pihrt-com/playoff/Playoff app/playoff.py

#!/usr/bin/env python
# playoff.py
# -*- coding: utf-8 -*-
__author__ = 'Martin Pihrt'

APP_current       = "1.0.11"                                         # current version of the application
APP_date          = "23.06.2026-08:15"                               # current version date  
update_check_link = "https://raw.githubusercontent.com/pihrt-com/playoff/refs/heads/main/Playoff%20app/version.json"    # path to JSON with APP version

import tkinter as tk
from tkinter import ttk, simpledialog, messagebox, filedialog, colorchooser
from tkinter import font as tkfont

import math, json, os, sys
import urllib.request
import time

try:
    from reportlab.pdfgen import canvas as rl_canvas
    from reportlab.lib.pagesizes import A4, landscape
    from reportlab.lib.colors import HexColor, black
    from reportlab.pdfbase import pdfmetrics
    from reportlab.pdfbase.ttfonts import TTFont
except ImportError:
    messagebox.showerror(
        "Chyba",
        "Pro vektorový PDF export je potřeba knihovna reportlab:\n\npip install reportlab"
    )

try:
    from openpyxl import Workbook, load_workbook
except ImportError:
    messagebox.showerror(
        "Chyba",
        "Pro import/export excell je potřeba knihovna openpyxl:\n\npip install openpyxl"
    )    

# universal path to resources (works in Python and PyInstaller EXE)
if getattr(sys, 'frozen', False):
    BASE_PATH = sys._MEIPASS
else:
    BASE_PATH = os.path.abspath(os.path.dirname(__file__))

# Pillow optional
try:
    from PIL import Image, ImageDraw, ImageFont, ImageTk
    PIL_AVAILABLE = True
except Exception:
    PIL_AVAILABLE = False

# try import usb_module (the new module we added). If missing, we provide a stub.
# Always add the current folder to sys.path so that the local usb_module.py is loaded.
sys.path.insert(0, os.path.dirname(os.path.abspath(__file__)))

try:
    import usb_module   # C:\Playoff\usb_module.py
    USB_AVAILABLE = True
except Exception as e:
    self._log("USB module error:", e)
    usb_module = None
    USB_AVAILABLE = False

# default settings
DEFAULT_BOX_W = 180
DEFAULT_BOX_H = 30
DEFAULT_H_GAP = 200
DEFAULT_V_GAP = 10
LINE_COLOR = "#0b6bd6"              # blue color
THIRD_PLACE_LINE_COLOR = "#d62828"  # red color
BOX_FILL = "#ffffff"
BOX_OUTLINE = "#000000"
TITLE_COLOR = "#000000"
CANVAS_BG_DEFAULT = "#ffffff"
# vítěz
WINNER_FILL = "#ffe06a"
WINNER_OUTLINE = "#cc9a00"
WINNER_TEXT_COLOR = "#000000"

# Default USB settings defaults (kept in setup file)
DEFAULT_USB_PORT           = ""
DEFAULT_USB_BAUD           = 115200
DEFAULT_USB_TIMEOUT        = 10.0

DEFAULT_USB_DISPLAY_A_BAUD = 115200
DEFAULT_USB_DISPLAY_B_BAUD = 115200

# --- Data classes ---
class Slot:
    def __init__(self, text=""):
        self.text = text

class Match:
    def __init__(self, a=None, b=None):
        self.a = a if a else Slot()
        self.b = b if b else Slot()

class Bracket:
    def __init__(self, team_list, pre_round_list, use_pre_round=False):
        """team_list: list of initial team names (may be empty strings)"""
        self.use_pre_round = use_pre_round
        self.team_count = max(0, int(len(team_list)))
        self.pre_count = max(0, int(len(pre_round_list)))
        self.rounds = []  # list of lists of Match
        self.titles = []
        self.pre_rounds = []
        self.pre_titles = []
        if use_pre_round:
            self._build_pre(pre_round_list)
        self._build(team_list)

    def _build_pre(self, pre_round_list):
        self.pre_rounds = []
        self.pre_titles = ["Předkolo"]
        first_round_match_count = math.ceil(len(pre_round_list) / 2)
        matches = []
        for i in range(first_round_match_count):
            matches.append(Match(Slot(""), Slot("")))
        self.pre_rounds.append(matches)

    def _build(self, team_list):
        self.rounds = []
        self.titles = []
        # initial round: pair teams sequentially, allowing last single
        teams = list(team_list)
        teams = [str(t) if t is not None else "" for t in teams]

        # first round matches: ceil(n/2)
        first_matches = math.ceil(len(teams) / 2) if len(teams) > 0 else 1
        matches0 = []
        for i in range(first_matches):
            a_idx = 2 * i
            b_idx = 2 * i + 1
            a = Slot(teams[a_idx]) if a_idx < len(teams) else Slot("")
            b = Slot(teams[b_idx]) if b_idx < len(teams) else Slot("")
            matches0.append(Match(a, b))
        self.rounds.append(matches0)
        self.titles.append("Kolo 1")

        # build subsequent rounds until 1 match
        prev_matches = matches0
        r = 1
        while len(prev_matches) > 1:
            next_count = math.ceil(len(prev_matches) / 2)
            next_matches = [Match() for _ in range(next_count)]
            self.rounds.append(next_matches)
            # default title
            if next_count == 1:
                self.titles.append("Finále")
            else:
                self.titles.append(f"Kolo {r+1}")
            prev_matches = next_matches
            r += 1
        # --- Winner ---
        # last real round = final → add a round with one slot
        winner_match = Match(Slot(""), Slot(""))
        self.rounds.append([winner_match])
        self.titles.append("Vítěz")            

    def rounds_count(self):
        return len(self.rounds)

# --- App ---
class PlayoffApp:
    def __init__(self, root):
        self.root = root
        root.title("Playoff generátor by Martin Pihrt © www.pihrt.com")

        # state
        self.bracket = None
        self.current_winner = ""
        self.bg_path = None
        self.bg_image = None
        self.bg_tk = None
        self.canvas_bg = CANVAS_BG_DEFAULT
        self.line_width = 2           # normal/thick
        self.font_scale = "large"     # small/medium/large
        self.odd_behavior = "manual"  # auto/manual/waiting
        self.lock_edit = False
        self.projector_mode = False
        self.enable_timer = True
        self.timer_value = '05:00'
        self.timer_running = False
        self.timer_blink = False
        self.current_seconds = 0
        self.timer_start_mode = "ok"  # "start" | "ok"  
        self.team_names = []          # Team naming database
        self.pre_round_enabled = True
        self.third_place_enabled = True
        self.third_place_title = "3. místo"
        self.lap_timer_enabled = True
        self.lap_timer_var = tk.BooleanVar(value=self.lap_timer_enabled)
        self.lap_time_a = 0   # ms
        self.lap_time_b = 0   # ms
        self.lap_time_a_var = tk.StringVar(value="A 00:00:000")
        self.lap_time_b_var = tk.StringVar(value="B 00:00:000")
        self.lap_running_a = False
        self.lap_running_b = False
        self.lap_after_id = None        
        self.font_scale_var = tk.StringVar(value=self.font_scale)
        self.odd_behavior_var = tk.StringVar(value=self.odd_behavior)
        self.line_width_var = tk.IntVar(value=self.line_width)
        self.timer_menu_var = tk.BooleanVar(value=self.enable_timer)
        self.timer_start_mode_var = tk.StringVar(value=self.timer_start_mode)
        self.pre_round_var = tk.BooleanVar(value=self.pre_round_enabled)
        self.third_place_var = tk.BooleanVar(value=self.third_place_enabled)

        self.third_place = {"a": "", "b": "", "winner": ""}        

        # USB manager (from usb_module)
        if USB_AVAILABLE:
            try:
                self.usb = usb_module.USBManager(self)
            except Exception:
                self.usb = None
        else:
            self.usb = None
        # store usb settings for saving into setup file
        self.usb_port = DEFAULT_USB_PORT
        self.usb_baud = DEFAULT_USB_BAUD
        self.usb_timeout = DEFAULT_USB_TIMEOUT

        # 7 seg LED display
        self.display_port_a = ""
        self.display_port_b = ""
        self.display_baud_a = DEFAULT_USB_DISPLAY_A_BAUD
        self.display_baud_b = DEFAULT_USB_DISPLAY_B_BAUD

        # view mode
        self.view_mode = "playoff"
        self.view_mode_var = tk.StringVar(value=self.view_mode)
        
        # laps mode data
        self.laps_a = []
        self.laps_b = []
        self.lap_id_a = 1
        self.lap_id_b = 1

        # Top toolbar: left settings (calls existing menu), right Start button and status label
        toolbar = tk.Frame(root)
        toolbar.pack(side='top', fill='x', padx=4, pady=4)

        # --- Settings icon (gear wheel) ---
        try:
            settings_img_path = os.path.join(BASE_PATH, "settings.ico")

            if PIL_AVAILABLE:
                img = Image.open(settings_img_path)

                if hasattr(img, "n_frames"):
                    best_pixels = 0
                    best_frame = 0
                    for i in range(img.n_frames):
                        img.seek(i)
                        w, h = img.size
                        if w * h > best_pixels:
                            best_pixels = w * h
                            best_frame = i
                    img.seek(best_frame)

                TARGET_H = 44

                w, h = img.size
                scale = TARGET_H / h
                new_w = int(w * scale)
                new_h = int(h * scale)

                img = img.resize((new_w, new_h), Image.LANCZOS)
                settings_raw = ImageTk.PhotoImage(img)

            else:
                # fallback bez Pillow
                settings_raw = tk.PhotoImage(file=settings_img_path)

            self.settings_btn = tk.Menubutton(toolbar, image=settings_raw, relief=tk.FLAT)
            self.settings_btn.image = settings_raw  # nutné pro garbage-collector

            self.settings_menu = tk.Menu(self.settings_btn, tearoff=0)
            self.settings_btn.config(menu=self.settings_menu)
            self.settings_btn.pack(side='left', padx=4)

            ver_txt = f"app verze: {APP_current} ({APP_date})"
            self.ver_label = tk.Label(toolbar, text=ver_txt, fg="#666666", font=("Arial", 7))
            self.ver_label.pack(side='left', padx=(10,0))

            # --- USB STATUS INDICATOR ---
            self.usb_status_canvas = tk.Canvas(toolbar, width=12, height=12, highlightthickness=0, bd=0, bg=toolbar.cget("bg"))
            self.usb_status_id = self.usb_status_canvas.create_oval(2, 2, 10, 10, fill="red", outline="red")
            self.usb_status_canvas.pack(side="left", padx=(10, 2))

            self.usb_status_label = tk.Label(toolbar, text="USB", fg="#333333", font=("Arial", 8, "bold"))
            self.usb_status_label.pack(side="left", padx=(0, 10))

            # --- DISPLAY ID-1 STATUS ---
            self.disp1_status_canvas = tk.Canvas(
                toolbar,
                width=12,
                height=12,
                highlightthickness=0,
                bd=0,
                bg=toolbar.cget("bg")
            )

            self.disp1_status_id = self.disp1_status_canvas.create_oval(
                2, 2, 10, 10,
                fill="red",
                outline="red"
            )

            self.disp1_status_canvas.pack(side="left", padx=(5, 2))

            self.disp1_status_label = tk.Label(
                toolbar,
                text="ID1",
                fg="#333333",
                font=("Arial", 8, "bold")
            )

            self.disp1_status_label.pack(side="left", padx=(0, 10))


            # --- DISPLAY ID-2 STATUS ---
            self.disp2_status_canvas = tk.Canvas(
                toolbar,
                width=12,
                height=12,
                highlightthickness=0,
                bd=0,
                bg=toolbar.cget("bg")
            )

            self.disp2_status_id = self.disp2_status_canvas.create_oval(
                2, 2, 10, 10,
                fill="red",
                outline="red"
            )

            self.disp2_status_canvas.pack(side="left", padx=(5, 2))

            self.disp2_status_label = tk.Label(
                toolbar,
                text="ID2",
                fg="#333333",
                font=("Arial", 8, "bold")
            )

            self.disp2_status_label.pack(side="left", padx=(0, 10))

            # --------------------------------------------------
            # VIEW MODE
            # --------------------------------------------------
            self.mode_frame = tk.Frame(toolbar)

            self.mode_frame.pack(
                side="left",
                padx=(20, 20)
            )

            self.mode_playoff_btn = tk.Label(
                self.mode_frame,
                text="PLAYOFF",
                width=10,
                relief="raised",
                bd=2,
                cursor="hand2",
                padx=8,
                pady=3
            )

            self.mode_playoff_btn.pack(
                side="left",
                padx=(0, 2)
            )

            self.mode_laps_btn = tk.Label(
                self.mode_frame,
                text="LAPS",
                width=10,
                relief="raised",
                bd=2,
                cursor="hand2",
                padx=8,
                pady=3
            )

            self.mode_laps_btn.pack(
                side="left"
            )

            self.mode_playoff_btn.bind(
                "<Button-1>",
                lambda e: self.change_view_mode("playoff")
            )

            self.mode_laps_btn.bind(
                "<Button-1>",
                lambda e: self.change_view_mode("laps")
            )

            self.update_view_mode_buttons()

        except Exception as e:
            self._log("Nelze načíst settings ikonu:", e)
            self.settings_btn = tk.Menubutton(toolbar, text="⚙", relief=tk.RAISED)
            self.settings_menu = tk.Menu(self.settings_btn, tearoff=0)
            self.settings_btn.config(menu=self.settings_menu)
            self.settings_btn.pack(side='left')

            ver_txt = f"app verze: {APP_current} ({APP_date})"
            self.ver_label = tk.Label(toolbar, text=ver_txt, fg="#666666", font=("Arial", 7))
            self.ver_label.pack(side='left', padx=(10,0))


        # teams
        self.settings_menu.add_command(label='Počet týmů', command=self.ask_team_count)
        self.settings_menu.add_command(label='Generovat týmy', command=self.generate_from_entry)
        self.settings_menu.add_command(label='Pojmenování týmů', command=self.open_team_naming_dialog)
        self.settings_menu.add_command(label='Smazat jen obsah', command=self.reset_values)
        self.settings_menu.add_command(label='Vymazat všechno', command=self.clear_all)
        self.settings_menu.add_checkbutton(label='Používat předkolo', variable=self.pre_round_var, command=self.toggle_pre_round)
        self.settings_menu.add_checkbutton(label='Zobrazit 3. místo', variable=self.third_place_var, command=self.toggle_third_place)

        # odd behavior
        odd_menu = tk.Menu(self.settings_menu, tearoff=0)
        self.settings_menu.add_cascade(label='Chování při lichém počtu vítězů', menu=odd_menu)        
        odd_menu.add_radiobutton(
            label='Automatický BYE',
            variable=self.odd_behavior_var,
            value='auto',
            command=lambda: self.set_odd_behavior('auto')
        )

        odd_menu.add_radiobutton(
            label='Ruční postup',
            variable=self.odd_behavior_var,
            value='manual',
            command=lambda: self.set_odd_behavior('manual')
        )

        odd_menu.add_radiobutton(
            label='Čekající hráč',
            variable=self.odd_behavior_var,
            value='waiting',
            command=lambda: self.set_odd_behavior('waiting')
        )

        self.settings_menu.add_separator()
        self.settings_menu.add_command(label='Načíst pozadí', command=self.load_bg_image)
        self.settings_menu.add_command(label='Smazat pozadí', command=self.remove_bg)

        # font submenu
        font_menu = tk.Menu(self.settings_menu, tearoff=0)
        self.settings_menu.add_cascade(label='Velikost písma', menu=font_menu)        
        font_menu.add_radiobutton(
            label='Malé',
            variable=self.font_scale_var,
            value='small',
            command=lambda: self.set_font_scale('small')
        )

        font_menu.add_radiobutton(
            label='Střední',
            variable=self.font_scale_var,
            value='medium',
            command=lambda: self.set_font_scale('medium')
        )

        font_menu.add_radiobutton(
            label='Velké',
            variable=self.font_scale_var,
            value='large',
            command=lambda: self.set_font_scale('large')
        )
    
        self.settings_menu.add_command(label='Barva pozadí', command=self.choose_canvas_bg)

        # line width submenu
        lw_menu = tk.Menu(self.settings_menu, tearoff=0)
        self.settings_menu.add_cascade(label='Tloušťka čar', menu=lw_menu)
        lw_menu.add_radiobutton(
            label='Normální',
            variable=self.line_width_var,
            value=2,
            command=lambda: self.set_line_width(2)
        )

        lw_menu.add_radiobutton(
            label='Silné',
            variable=self.line_width_var,
            value=4,
            command=lambda: self.set_line_width(4)
        )

        self.settings_menu.add_separator()
        self.settings_menu.add_checkbutton(label='Zamknout editaci týmů', command=self.toggle_lock_edit)
        self.settings_menu.add_command(label='Načíst ze souboru', command=self.load_setup)
        self.settings_menu.add_command(label='Uložit do souboru', command=self.save_setup)

        # timer enable
        self.settings_menu.add_separator()        
        self.timer_menu_var = tk.BooleanVar(value=self.enable_timer)
        self.settings_menu.add_checkbutton(label='Povolit odpočet', variable=self.timer_menu_var, command=self.on_toggle_timer)

        # timer mode
        timer_mode_menu = tk.Menu(self.settings_menu, tearoff=0)
        self.settings_menu.add_cascade(label='Režim spuštění odpočtu', menu=timer_mode_menu)

        timer_mode_menu.add_radiobutton(
            label='Spustit odpočet ihned (po START)',
            variable=self.timer_start_mode_var,
            value='start',
            command=lambda: self.set_timer_start_mode('start')
        )

        timer_mode_menu.add_radiobutton(
            label='Spustit odpočet až po semaforu (OK)',
            variable=self.timer_start_mode_var,
            value='ok',
            command=lambda: self.set_timer_start_mode('ok')
        )

        self.settings_menu.add_checkbutton(
            label='Měřit a zobrazit čas kola',
            variable=self.lap_timer_var,
            command=self.on_toggle_lap_timer
        )

        self.settings_menu.add_separator()
        self.settings_menu.add_command(label='USB nastavení', command=self.open_usb_dialog)

        self.settings_menu.add_separator()
        self.settings_menu.add_command(label='Export do PDF', command=self.export_pdf)

        # Fullscreen mode toggle
        self.fullscreen_var = tk.BooleanVar(value=self.projector_mode)
        self.settings_menu.add_checkbutton(
            label='Celá obrazovka',
            variable=self.fullscreen_var,
            command=self.toggle_projector
        )

        self.settings_menu.add_command(label='Nápověda', command=self.show_help)
        
        self.settings_menu.add_command(label='Kontrola aktualizace', command=self.check_for_update)

        self.settings_btn.config(menu=self.settings_menu)
        self.settings_btn.pack(side='left')

        spacer = tk.Label(toolbar, text='')
        spacer.pack(side='left', expand=True)

        # ----- LAP TIMERS (A/B) -----
        self.lap_label_a = tk.Label(
            toolbar,
            textvariable=self.lap_time_a_var,
            font=("Consolas", 22, "bold"),
            fg="#FF8C00",
            bg="black",
            relief="ridge",
            bd=3,
            padx=12,
            pady=4
        )

        self.lap_label_b = tk.Label(
            toolbar,
            textvariable=self.lap_time_b_var,
            font=("Consolas", 22, "bold"),
            fg="#FF8C00",
            bg="black",
            relief="ridge",
            bd=3,
            padx=12,
            pady=4
        )

        # default hidden
        self.lap_label_a.pack_forget()
        self.lap_label_b.pack_forget()

        # ----- Live time and date -----
        self.datetime_var = tk.StringVar(value="")
        self.datetime_label = tk.Label(toolbar, textvariable=self.datetime_var, font=("Consolas", 22, "bold"))
        self.datetime_label.pack(side='left', expand=True)

        # status label at right
        self.status_var = tk.StringVar(value='')
        self.status_label = tk.Label(toolbar, textvariable=self.status_var)
        self.status_label.pack(side='right', padx=(0,8))

        # Start button
        self.start_btn = tk.Button(
            toolbar,
            text='Start',
            command=self.on_start,
            font=("Arial", 12, "bold"),   # ← larger and bold text
            padx=15,                      # ← horizontal padding
            pady=5                        # ← vertical padding
        )

        self.start_btn.pack(side='right', padx=4)
        if not USB_AVAILABLE:
            self.start_btn.config(state='disabled')
            self.status_var.set('USB modul chybí')

        # top controls
        self.team_var = tk.StringVar(value="16")

        # canvas
        self.canvas = tk.Canvas(root, bg=self.canvas_bg)
        self.canvas.pack(fill="both", expand=True)
        self.canvas.bind('<Configure>', lambda e: self.redraw())

        # Timer overlay (canvas create_window)
        self.timer_label = tk.Label( # timer MM:SS box size
            self.root, 
            text=self.timer_value,
            font=("Consolas", 100, "bold"), 
            bg='black', 
            fg='white',
            bd=4,         # larger margin
            relief='ridge',
            padx=20,      # horizontal inner edge
            pady=10       # vertical inner edge
        ) 
        self.timer_label.bind('<Button-3>', self.on_timer_right_click)
        self.timer_window = None

        self.rect_items = {}
        self.text_items = {}
        self.title_items = {}
        self.line_items = []

        # initial bracket: empty list of N empty team slots based on team_var
        try:
            n = int(self.team_var.get())
        except Exception:
            n = 16

        self.update_datetime()
        self.on_toggle_lap_timer()
        self.check_for_update()
        
        # automatic USB check every 1.5 s
        self.root.after(1500, self.auto_check_usb)

        root.bind('<Escape>', lambda e: self.exit_fullscreen())

        # try load usb settings from previous setup file if available
        try:
            settings_path = os.path.join(
                os.path.expanduser('~'),
                '.playoff_settings.json'
            )

            if os.path.exists(settings_path):
                with open(settings_path, 'r', encoding='utf-8') as f:
                    s = json.load(f)

                self.usb_port = s.get('usb_port', self.usb_port)
                self.usb_baud = s.get('usb_baud', self.usb_baud)
                self.usb_timeout = s.get('usb_timeout', self.usb_timeout)
                self.display_port_a = s.get('display_port_a', self.display_port_a)
                self.display_port_b = s.get('display_port_b', self.display_port_b)
                self.display_baud_a = s.get('display_baud_a', self.display_baud_a)
                self.display_baud_b = s.get('display_baud_b', self.display_baud_b)

                self.view_mode = s.get('view_mode', 'playoff')
                self.view_mode_var.set(self.view_mode)

                self.root.after(100, self.update_view_mode_gui)

                try:
                    self.update_view_mode_buttons()
                except:
                    pass

                # LED panel status
                if self.display_port_a:
                    self.update_display_status(1, True)
                else:
                    self.update_display_status(1, False)

                if self.display_port_b:
                    self.update_display_status(2, True)
                else:
                    self.update_display_status(2, False)                

                if self.usb and self.usb_port:
                    try:
                        self.usb.validate_and_set(
                            self.usb_port,
                            self.usb_baud,
                            self.usb_timeout
                        )

                        # CONNECT
                        self.usb.connect()

                        # START RX THREAD
                        self.usb.start_reader(self.on_usb_line)
                        self.usb.connect_displays()
                        self.update_usb_status(True)
                        self._log(f"USB AUTO CONNECT: port { self.usb_port} speed {self.usb_baud}")
                        self.root.after(
                            2500,
                            lambda: self.usb.send_display(1, "TXT:ID-1")
                        )
                        self.root.after(
                            2600,
                            lambda: self.usb.send_display(2, "TXT:ID-2")
                        )                
                        self.root.after(
                            7000,
                            lambda: self.usb.send_display(1, "TXT:-------")
                        )
                        self.root.after(
                            7200,
                            lambda: self.usb.send_display(2, "TXT:-------")
                        )                        
                        if self.view_mode == "laps":
                            self.usb.handler.send(b"mode_laps\n")
                        else:
                            self.usb.handler.send(b"mode_playoff\n")

                    except Exception as e:
                        self._log("USB AUTO CONNECT ERROR:", e)
                        self.update_usb_status(False)

        except Exception as e:
            self._log("USB SETTINGS LOAD ERROR:", e)

    def _now(self):
        return time.strftime("%H:%M:%S")

    def _log(self, msg: str, param=""):
        print(f"[playoff {self._now()}] {msg} {param}", file=sys.stderr)

    def on_close(self):
        if self.usb:
            self.usb.disconnect_displays()
            self.usb.disconnect()
        self.root.destroy()

    def update_third_place_from_semifinal(self):
        if not self.bracket or not self.third_place_enabled:
            return

        rounds = self.bracket.rounds

        if len(rounds) < 3:
            return

        semifinal_round = len(rounds) - 3
        final_round = len(rounds) - 2

        semifinal_matches = rounds[semifinal_round]
        final_match = rounds[final_round][0]

        losers = []

        for m_idx, match in enumerate(semifinal_matches):
            a = match.a.text.strip()
            b = match.b.text.strip()

            finalist_a = final_match.a.text.strip()
            finalist_b = final_match.b.text.strip()

            if a == finalist_a or a == finalist_b:
                loser = b
            elif b == finalist_a or b == finalist_b:
                loser = a
            else:
                loser = ""

            if loser:
                losers.append(loser)

        if len(losers) >= 2:
            self.third_place["a"] = losers[0]
            self.third_place["b"] = losers[1]


    def toggle_pre_round(self):
        self.pre_round_enabled = self.pre_round_var.get()
        if not self.bracket:
            self.redraw()
            return

        if self.pre_round_enabled:
            if not self.bracket.pre_rounds:
                n = self.bracket.team_count
                pre_round_list = [""] * n
                self.bracket._build_pre(pre_round_list)
        else:
            pass

        self.redraw()

    def check_for_update(self):
        try:
            with urllib.request.urlopen(update_check_link, timeout=3) as r:
                info = json.loads(r.read().decode('utf-8'))
        except:
            messagebox.showwarning("Aktualizace programu", "Nepodařilo se stáhnout data z Internetu.")
            return

        latest = info.get("version")
        url = info.get("url")

        if latest != APP_current:
            if messagebox.askyesno("Aktualizace programu", f"Dostupná verze {latest}. Aktualizovat?"):
                # path to the file to be updated
                if getattr(sys, 'frozen', False):
                    # runs as EXE
                    exe_path = sys.executable
                    app_dir = os.path.dirname(sys.executable)
                else:
                    # runs as .py
                    exe_path = os.path.abspath(__file__)
                    app_dir = os.path.dirname(exe_path)

                updater = os.path.join(app_dir, "updater.exe")

                import subprocess
                try:
                    subprocess.Popen([updater, exe_path, url], close_fds=True)
                except Exception as e:
                    messagebox.showerror("Updater chyba", f"Nelze spustit updater.exe:\n{e}")
                    return

                self.root.destroy()
                sys.exit(0)

        else:
            messagebox.showinfo("Aktualizace", "Máte nejnovější verzi :-)")

    def edit_pre_title(self):
        if self.lock_edit:
            return

        current = self.bracket.pre_titles[0] if self.bracket.pre_titles else "Předkolo"

        dlg = tk.Toplevel(self.root)
        dlg.title("Změnit nadpis předkola")
        dlg.transient(self.root)
        dlg.grab_set()

        tk.Label(dlg, text="Nadpis:").pack(padx=10, pady=(10,4))
        ent = tk.Entry(dlg, width=40)
        ent.insert(0, current)
        ent.pack(padx=10, pady=6)
        ent.focus_set()

        def on_ok():
            new = ent.get().strip()
            if not self.bracket.pre_titles:
                self.bracket.pre_titles = [new]
            else:
                self.bracket.pre_titles[0] = new
            dlg.destroy()
            self.redraw()

        tk.Button(dlg, text="OK", command=on_ok).pack(pady=10)
        dlg.bind("<Return>", lambda e: on_ok())
        dlg.bind("<Escape>", lambda e: dlg.destroy())

        self.root.wait_window(dlg)

    def edit_pre_slot(self, m_idx, side):
        if self.lock_edit:
            return

        match = self.bracket.pre_rounds[0][m_idx]
        slot = match.a if side == 'a' else match.b

        dlg = tk.Toplevel(self.root)
        dlg.title("Zadej tým (Předkolo)")
        dlg.transient(self.root)
        dlg.grab_set()

        tk.Label(dlg, text="Zadej číslo nebo název týmu:").pack(padx=10, pady=(10, 4))
        ent = tk.Entry(dlg, width=40)
        ent.pack(padx=10, pady=6)
        ent.insert(0, slot.text)
        ent.focus_set()

        def on_ok():
            slot.text = ent.get()
            dlg.destroy()
            self.redraw()

        tk.Button(dlg, text="OK", command=on_ok).pack(pady=10)
        dlg.bind("<Return>", lambda e: on_ok())
        dlg.bind("<Escape>", lambda e: dlg.destroy())

        self.root.wait_window(dlg)    

    def ask_team_count(self):
        dlg = tk.Toplevel(self.root)
        dlg.title("Zadat počet týmů")
        dlg.transient(self.root)
        dlg.grab_set()

        tk.Label(dlg, text="Počet týmů:").pack(padx=10, pady=6)
        ent = tk.Entry(dlg, width=10)
        ent.insert(0, self.team_var.get())
        ent.pack(padx=10, pady=4)
        ent.focus_set()

        def on_ok():
            val = ent.get()
            if not val.isdigit() or int(val) < 1:
                messagebox.showerror("Chyba", "Počet týmů musí být kladné číslo.")
                return

            if not val.isdigit() or int(val) > 24:
                messagebox.showerror("Chyba", "Počet týmů musí být <= 24.")
                return                

            self.team_var.set(val)
            dlg.destroy()

            self.generate_bracket_with_empty(int(val))

        tk.Button(dlg, text="OK", command=on_ok).pack(pady=8)
        dlg.bind("<Return>", lambda e: on_ok())
        dlg.bind("<Escape>", lambda e: dlg.destroy())
    
    def update_datetime(self):
        import datetime
        now = datetime.datetime.now()
        self.datetime_var.set(now.strftime("%d.%m.%Y  %H:%M:%S"))
        self.root.after(1000, self.update_datetime)

    def start_lap_timer(self):
        self.lap_running_a = True
        self.lap_running_b = True

        if self.lap_after_id:
            try:
                self.root.after_cancel(self.lap_after_id)
            except:
                pass

        import time
        self.lap_last_time = time.time()

        self.lap_loop()

    def lap_loop(self):
        import time

        if not self.lap_running_a and not self.lap_running_b:
            return

        now = time.time()
        delta = now - self.lap_last_time
        self.lap_last_time = now

        delta_ms = int(delta * 1000)

        if self.lap_running_a:
            self.lap_time_a += delta_ms

        if self.lap_running_b:
            self.lap_time_b += delta_ms

        self.lap_time_a_var.set("A " + self.format_lap(self.lap_time_a))
        self.lap_time_b_var.set("B " + self.format_lap(self.lap_time_b))

        self.lap_after_id = self.root.after(50, self.lap_loop)

    def format_lap(self, ms):
        minutes = ms // 60000
        seconds = (ms % 60000) // 1000
        millis = ms % 1000
        return f"{minutes:02d}:{seconds:02d}:{millis:03d}"

    def start_laps_timer(self):
        import time
        if self.lap_after_id:
            try:
                self.root.after_cancel(self.lap_after_id)
            except:
                pass
        self.lap_last_time = time.time()
        self.lap_after_id = self.root.after(50, self.laps_loop)        

    def laps_loop(self):
        import time
        if not self.lap_running_a and not self.lap_running_b:
            self.lap_after_id = None
            return

        now = time.time()
        delta = now - self.lap_last_time
        self.lap_last_time = now
        delta_ms = int(delta * 1000)
        if self.lap_running_a:
            self.lap_time_a += delta_ms
        if self.lap_running_b:
            self.lap_time_b += delta_ms
        self.lap_time_a_var.set(
            "A " + self.format_lap(self.lap_time_a)
        )
        self.lap_time_b_var.set(
            "B " + self.format_lap(self.lap_time_b)
        )
        self.lap_after_id = self.root.after(50, self.laps_loop)

    def finish_a(self):
        if not self.lap_running_a:
            return

        self._log("FINISH A")
        self.lap_running_a = False
        self.lap_label_a.config(fg="green")


    def finish_b(self):
        if not self.lap_running_b:
            return

        self._log("FINISH B")
        self.lap_running_b = False
        self.lap_label_b.config(fg="green")


    def format_display_time(self, ms):
        total_seconds = ms / 1000.0
        # 00.000 to 59.999
        if total_seconds < 60:
            return f"{total_seconds:06.3f}"
        # 01.00.0 to 99.59.9
        minutes = int(total_seconds // 60)
        seconds = int(total_seconds % 60)
        tenths = int((total_seconds * 10) % 10)
        return f"{minutes:02d}.{seconds:02d}.{tenths}"

    # small helper to open the existing settings menu -> we will just show the menubar cascade
    def _open_menu_settings(self):
        # open ask_team_count as a representative settings entry
        try:
            self.ask_team_count()
        except Exception:
            pass

    def update_usb_status(self, connected: bool):
        """GRN = connected, RED = disconnected."""
        try:
            color = "green" if connected else "red"
            self.usb_status_canvas.itemconfig(self.usb_status_id, fill=color, outline=color)
        except:
            pass

    def on_view_mode_change(self):
        new_mode = self.view_mode_var.get()
        if new_mode == self.view_mode:
            return

        if not messagebox.askyesno(
            "Změna režimu",
            f"Opravdu přepnout do režimu "
            f"{new_mode.upper()} ?"
        ):
            self.view_mode_var.set(self.view_mode)
            return

        self.view_mode = new_mode
        self.update_view_mode_gui()
        self._log(f"VIEW MODE = {self.view_mode}")
        self.redraw()
        try:
            if self.usb:
                if self.view_mode == "laps":
                    self.usb.handler.send(b"mode_laps\n")
                else:
                    self.usb.handler.send(b"mode_playoff\n")
        except Exception as e:
            self._log(f"MODE SEND ERROR: {e}")        

    def change_view_mode(self, new_mode):
        if new_mode == self.view_mode:
            return

        if not messagebox.askyesno(
            "Změna režimu",
            f"Opravdu přepnout do režimu "
            f"{new_mode.upper()} ?"
        ):
            return

        self.lap_time_a = 0
        self.lap_time_b = 0
        self.lap_running_a = False
        self.lap_running_b = False
        self.lap_after_id = None
        self.view_mode = new_mode
        self.view_mode_var.set(new_mode)
        self.update_view_mode_buttons()
        self.update_view_mode_gui()
        self._log(f"VIEW MODE = {self.view_mode}")
        if new_mode == "laps":
            self.status_var.set("")
        self.root.update_idletasks()
        self.canvas.update_idletasks()
        self.redraw()
        try:
            if self.usb:
                if self.view_mode == "laps":
                    self._log("TX mode_laps")
                    self.usb.handler.send(b"mode_laps\n")
                else:
                    self._log("TX mode_playoff")
                    self.usb.handler.send(b"mode_playoff\n")
        except Exception as e:
            self._log(f"MODE SEND ERROR: {e}")        

    def update_view_mode_buttons(self):
        if self.view_mode == "playoff":
            self.mode_playoff_btn.config(
                bg="#4CAF50",
                fg="white",
                relief="sunken"
            )

            self.mode_laps_btn.config(
                bg=self.root.cget("bg"),
                fg="black",
                relief="raised"
            )
        else:
            self.mode_laps_btn.config(
                bg="#4CAF50",
                fg="white",
                relief="sunken"
            )

            self.mode_playoff_btn.config(
                bg=self.root.cget("bg"),
                fg="black",
                relief="raised"
            )

    def update_view_mode_gui(self):
        self.start_btn.pack_forget()
        if self.view_mode == "playoff":
            self.start_btn.pack(side='right', padx=4)               

    def update_display_status(self, disp_id, connected):
        try:
            color = "green" if connected else "red"
            if disp_id == 1:
                self.disp1_status_canvas.itemconfig(self.disp1_status_id, fill=color, outline=color)
            elif disp_id == 2:
                self.disp2_status_canvas.itemconfig(self.disp2_status_id, fill=color, outline=color)
        except:
            pass            

    def auto_check_displays(self):
        try:
            ports = self.usb.list_ports() if self.usb else []
            id1 = (
                self.display_port_a
                and self.display_port_a in ports
                and self.usb.display_a
                and self.usb.display_a.is_open
            )
        except:
            id1 = False

        try:
            id2 = (
                self.display_port_b
                and self.display_port_b in ports
                and self.usb.display_b
                and self.usb.display_b.is_open
            )
        except:
            id2 = False

        self.update_display_status(1, id1)
        self.update_display_status(2, id2)

    def auto_check_usb(self):
        """Automatic USB port check."""
        try:
            if self.usb:
                ports = self.usb.list_ports()
                if self.usb_port and (self.usb_port not in ports):
                    self.update_usb_status(False)
                else:
                    if self.usb_port:
                        self.update_usb_status(True)
                    else:
                        self.update_usb_status(False)
        except Exception:
            self.update_usb_status(False)

        # refresh for 1500 ms
        self.root.after(1500, self.auto_check_usb)
        self.root.after(1500, self.auto_check_displays)

    def on_usb_line(self, line):
        line = line.strip().lower()
        self._log(f"USB RX: {repr(line)}")

        def gui():
            if line == "ok":
                self.status_var.set("Přijato OK")
                self.status_label.config(fg="green")   
                if self.enable_timer and self.timer_start_mode == "ok":
                    self.usb.send_display(1, "TXT:00.000")
                    self.usb.send_display(2, "TXT:00.000")
                    self.start_countdown()
                    self.lap_time_a = 0
                    self.lap_time_b = 0
                    self.lap_time_a_var.set("A 00:00:000")
                    self.lap_time_b_var.set("B 00:00:000")
                    if self.lap_timer_enabled:
                        self.start_lap_timer()

            elif line == "finish_a":
                self.finish_a()
                self.usb.send_display(1, f"TXT:{self.format_display_time(self.lap_time_a)}")

            elif line == "finish_b":
                self.finish_b()
                self.usb.send_display(2, f"TXT:{self.format_display_time(self.lap_time_b)}")

            elif line == "race_finished":
                if self.view_mode == "playoff":
                    self.status_var.set("Závod dokončen")
                    self.status_label.config(fg="blue")
                else:
                    self.status_var.set("")
                self.timer_running = False
                self.lap_running_a = False
                self.lap_running_b = False
                if self.lap_after_id:
                    try:
                        self.root.after_cancel(self.lap_after_id)
                    except:
                        pass
                    self.lap_after_id = None

            elif line == "start_a":
                self._log("LAPS START A")
                if self.view_mode == "laps":
                    self.usb.send_display(1, "TXT:00.000")
                    self.lap_label_a.config(fg="#FF8C00")
                    self.lap_time_a = 0
                    self.lap_running_a = True
                    self._log(f"lap_after_id={self.lap_after_id}")
                    self.start_laps_timer()

            elif line == "start_b":
                self._log("LAPS START B")
                if self.view_mode == "laps":
                    self.usb.send_display(2, "TXT:00.000")
                    self.lap_label_b.config(fg="#FF8C00")
                    self.lap_time_b = 0
                    self.lap_running_b = True
                    self._log(f"lap_after_id={self.lap_after_id}")
                    self.start_laps_timer()

            elif line == "stop_a":
                self._log("LAPS STOP A")
                self.lap_running_a = False
                if self.view_mode == "laps":
                    self.lap_label_a.config(fg="green")
                    from datetime import datetime
                    rec = {
                        "id": self.lap_id_a,
                        "date": datetime.now().strftime("%d.%m.%Y %H:%M:%S"),
                        "time": self.format_lap(self.lap_time_a),
                        "ms": self.lap_time_a
                    }
                    self.laps_a.insert(0, rec)
                    self.lap_id_a += 1
                    self.redraw()
                    self.usb.send_display(1, f"TXT:{self.format_display_time(self.lap_time_a)}")

            elif line == "stop_b":
                self._log("LAPS STOP B")
                self.lap_running_b = False
                if self.view_mode == "laps":
                    self.lap_label_b.config(fg="green")
                    from datetime import datetime
                    rec = {
                        "id": self.lap_id_b,
                        "date": datetime.now().strftime("%d.%m.%Y %H:%M:%S"),
                        "time": self.format_lap(self.lap_time_b),
                        "ms": self.lap_time_b
                    }
                    self.laps_b.insert(0, rec)
                    self.lap_id_b += 1
                    self.redraw() 
                    self.usb.send_display(2, f"TXT:{self.format_display_time(self.lap_time_b)}")               

        self.root.after(0, gui)        

    def on_start(self):
        self.lap_label_a.config(fg="#FF8C00")
        self.lap_label_b.config(fg="#FF8C00")
        self._log(f"usb_port= {self.usb_port} usb_baud= {self.usb_baud} usb_timeout= {self.usb_timeout} usb obj existuje: {bool(self.usb)} timer_start_mode= {self.timer_start_mode}")

        # STOP old countdown
        try:
            self.timer_running = False
            if getattr(self, 'countdown_after_id', None):
                self.root.after_cancel(self.countdown_after_id)
                self.countdown_after_id = None
        except Exception:
            pass

        # STOP old lap timer
        try:
            self.lap_running_a = False
            self.lap_running_b = False
            if self.lap_after_id:
                self.root.after_cancel(self.lap_after_id)
                self.lap_after_id = None

        except Exception:
            pass

        self.start_btn.config(state='disabled')

        self.status_var.set('Odesílám...')
        self.status_label.config(fg='black')

        # ---------------------------------------------------------
        # CALLBACK FROM USB MODULE
        # ---------------------------------------------------------
        def on_result(ok, reason):
            def cb():
                if ok:
                    # START packet was successfully sent
                    # WAITING FOR "ok" FROM ARDUINO
                    self.status_var.set('START odeslán')
                    self.status_label.config(fg='orange')
                    self.update_usb_status(True)

                else:
                    if reason == 'timeout':
                        self.status_var.set('Chyba spojení (timeout)')
                    elif isinstance(reason, str) and reason.startswith('open_error'):
                        self.status_var.set('Chyba spojení (otevření portu)')
                    elif reason == 'pyserial_missing':
                        self.status_var.set('pyserial není nainstalován')
                    else:
                        self.status_var.set('Chyba spojení (neznámá chyba)')
                    self.status_label.config(fg='red')
                    self.timer_running = False
                    self.update_usb_status(False)

                self.start_btn.config(state='normal')

            try:
                self.root.after(0, cb)

            except Exception:
                pass

        # ---------------------------------------------------------
        # PREPARE TIMER DISPLAY
        # ---------------------------------------------------------
        try:

            if self.enable_timer:

                self.current_seconds = self.time_to_seconds(self.timer_value)

                self.timer_label.config(
                    text=self.seconds_to_time(self.current_seconds)
                )

                # START MODE = start
                if self.timer_start_mode == 'start':

                    self.start_countdown()

                    # reset lap timer
                    self.lap_time_a = 0
                    self.lap_time_b = 0

                    self.lap_time_a_var.set("A 00:00:000")
                    self.lap_time_b_var.set("B 00:00:000")

                    if self.lap_timer_enabled:
                        self.start_lap_timer()

                else:

                    # MODE "ok"
                    # only prepare display
                    # countdown starts after RX "ok"

                    self.timer_running = False

        except Exception as e:
            self._log("Timer prepare error:", e)

        # ---------------------------------------------------------
        # SEND START
        # ---------------------------------------------------------
        try:

            usb_available = bool(self.usb and self.usb_port)

            if usb_available:

                self.usb.validate_and_set(
                    self.usb_port,
                    self.usb_baud,
                    self.usb_timeout
                )

                self.usb.send_start_async(on_result)

                self.update_usb_status(True)

            else:

                self.status_var.set('Chyba spojení')
                self.status_label.config(fg='red')

                self.timer_running = False

                self.update_usb_status(False)

                self.start_btn.config(state='normal')

        except Exception as e:

            self.status_var.set(f'Chyba: {e}')
            self.status_label.config(fg='red')

            self.timer_running = False

            self.start_btn.config(state='normal')

            self.update_usb_status(False)

    def open_team_naming_dialog(self):
        dlg = tk.Toplevel(self.root)
        dlg.title("Pojmenování týmů")
        dlg.transient(self.root)
        dlg.grab_set()
        dlg.geometry("700x500")

        # --- MAIN TEAM NAMES ---
        if not hasattr(self, "team_names"):
            self.team_names = []

        # --- SCROLL ---
        container = tk.Frame(dlg)
        container.pack(fill="both", expand=True, padx=10, pady=10)

        canvas = tk.Canvas(container, borderwidth=0, highlightthickness=0)
        scrollbar = tk.Scrollbar(container, orient="vertical", command=canvas.yview)
        scroll_frame = tk.Frame(canvas)

        scroll_frame.bind(
            "<Configure>",
            lambda e: canvas.configure(scrollregion=canvas.bbox("all"))
        )

        canvas.create_window((0, 0), window=scroll_frame, anchor="nw")
        canvas.configure(yscrollcommand=scrollbar.set)

        canvas.pack(side="left", fill="both", expand=True)
        scrollbar.pack(side="right", fill="y")

        scroll_frame.bind_all(
            "<MouseWheel>",
            lambda e: canvas.yview_scroll(int(-1*(e.delta/120)), "units")
        )

        # --- HEADS ---
        tk.Label(scroll_frame, text="ID týmu", font=("Arial", 10, "bold")).grid(row=0, column=0, padx=5, pady=5)
        tk.Label(scroll_frame, text="Popis týmu", font=("Arial", 10, "bold")).grid(row=0, column=1, padx=5, pady=5)
        tk.Label(scroll_frame, text="Akce", font=("Arial", 10, "bold")).grid(row=0, column=2, padx=5, pady=5)

        row_widgets = []

        def refresh_table():
            nonlocal row_widgets
            for w in row_widgets:
                for el in w:
                    el.destroy()
            row_widgets.clear()

            for i, item in enumerate(self.team_names):
                id_var = tk.StringVar(value=item.get("id", ""))
                desc_var = tk.StringVar(value=item.get("desc", ""))

                e1 = tk.Entry(scroll_frame, textvariable=id_var, width=10)
                e2 = tk.Entry(scroll_frame, textvariable=desc_var, width=40)

                e1.grid(row=i+1, column=0, padx=5, pady=2)
                e2.grid(row=i+1, column=1, padx=5, pady=2)

                def make_delete(idx):
                    return lambda: delete_row(idx)

                btn_del = tk.Button(scroll_frame, text="Smazat", command=make_delete(i))

                btn_del.grid(row=i+1, column=2, padx=5)

                def make_trace(index, var_id, var_desc):
                    def tracer(*args):
                        self.team_names[index]["id"] = var_id.get()
                        self.team_names[index]["desc"] = var_desc.get()
                    return tracer

                id_var.trace_add("write", make_trace(i, id_var, desc_var))
                desc_var.trace_add("write", make_trace(i, id_var, desc_var))

                row_widgets.append((e1, e2, btn_del))

        def add_row():
            self.team_names.append({"id": "", "desc": ""})
            refresh_table()

        def delete_row(index):
            if index < 0 or index >= len(self.team_names):
                return
            self.team_names.pop(index)
            refresh_table()

        def clear_all_rows():
            if not messagebox.askyesno("Potvrzení", "Opravdu chceš smazat všechny záznamy?"):
                return
            self.team_names.clear()
            refresh_table()

        def export_to_excel():
            if not self.team_names:
                messagebox.showinfo("Info", "Nejsou žádná data k exportu.")
                return

            path = filedialog.asksaveasfilename(
                defaultextension=".xlsx",
                filetypes=[("Excel", "*.xlsx")]
            )
            if not path:
                return

            wb = Workbook()
            ws = wb.active
            ws.title = "Pojmenování týmů"

            ws.append(["ID týmu", "Popis týmu"])

            for item in self.team_names:
                ws.append([item.get("id", ""), item.get("desc", "")])

            wb.save(path)
            messagebox.showinfo("Hotovo", f"Export dokončen:\n{path}")

        def import_from_excel():
            path = filedialog.askopenfilename(
                filetypes=[("Excel", "*.xlsx")]
            )
            if not path:
                return

            wb = load_workbook(path)
            ws = wb.active

            self.team_names.clear()

            for i, row in enumerate(ws.iter_rows(min_row=2, values_only=True)):
                if not row:
                    continue
                self.team_names.append({
                    "id": str(row[0]) if row[0] is not None else "",
                    "desc": str(row[1]) if row[1] is not None else ""
                })

            refresh_table()

        # --- BUTTONS ---
        btn_frame = tk.Frame(dlg)
        btn_frame.pack(fill="x", pady=8)

        tk.Button(btn_frame, text="Přidat řádek", command=add_row).pack(side="left", padx=5)
        tk.Button(btn_frame, text="Smazat vše", command=clear_all_rows).pack(side="left", padx=5)
        tk.Button(btn_frame, text="Import z Excelu", command=import_from_excel).pack(side="left", padx=5)
        tk.Button(btn_frame, text="Export do Excelu", command=export_to_excel).pack(side="left", padx=5)

        def on_save():
            dlg.destroy()
            self.redraw()

        tk.Button(btn_frame, text="Uložit", command=on_save).pack(side="right", padx=5)
        tk.Button(btn_frame, text="Storno", command=dlg.destroy).pack(side="right", padx=5)

        refresh_table()
        self.root.wait_window(dlg)


    # --- settings handlers ---
    def set_odd_behavior(self, mode):
        self.odd_behavior = mode
        self.odd_behavior_var.set(mode)
        self.redraw()

    def set_font_scale(self, size):
        self.font_scale = size
        self.font_scale_var.set(size)
        self.redraw()

    def choose_canvas_bg(self):
        c = colorchooser.askcolor()[1]
        if c:
            self.canvas_bg = c
            self.canvas.config(bg=self.canvas_bg)
            self.redraw()

    def set_line_width(self, w):
        self.line_width = w
        self.line_width_var.set(w)
        self.redraw()

    def toggle_lock_edit(self):
        self.lock_edit = not self.lock_edit
        messagebox.showinfo('Info', f'Zamknutí polí bylo provedeno: {self.lock_edit}')

    def set_timer_start_mode(self, mode):
        self.timer_start_mode = mode
        self.timer_start_mode_var.set(mode)

    def toggle_third_place(self):
        self.third_place_enabled = self.third_place_var.get()
        self.redraw()        

    # --- USB wrapper ---
    def open_usb_dialog(self):
        dlg = tk.Toplevel(self.root)
        dlg.title("USB spojení")
        dlg.transient(self.root)
        dlg.grab_set()
        w = 500; h = 650
        x = (dlg.winfo_screenwidth()-w)//2; y = (dlg.winfo_screenheight()-h)//2
        dlg.geometry(f"{w}x{h}+{x}+{y}")

        # --- PORTS LIST ---
        if self.usb:
            ports = self.usb.list_ports()
        else:
            ports = []

        def test_display(id = 0):
            try:
                if self.usb:
                    if id == 0:
                        self.usb.send_display(1, "CLS")
                        self.usb.send_display(2, "CLS")      
                    if id == 1:
                        self.usb.send_display(1, "TXT:ID-1")
                    if id == 2:
                        self.usb.send_display(2, "TXT:ID-2")                        

            except Exception as e:
                self._log(f"Display error {e}")
                messagebox.showerror("Displej chyba", str(e))

        # --- GATE A/B device ---
        tk.Label(dlg, text="Měřící brána", font=("Arial",10,"bold")).pack(anchor='w', padx=10, pady=(12,0))
        port_var = tk.StringVar(value=self.usb_port)
        combo = ttk.Combobox(
            dlg,
            textvariable=port_var,
            values=ports,
            state="readonly",
            width=20
        )
        combo.pack(padx=10, pady=4)

        frame = tk.Frame(dlg)
        frame.pack(fill='x', padx=10)

        # --- Preselect current port if available ---
        if self.usb_port in ports:
            port_var.set(self.usb_port)
        elif ports:
            port_var.set(ports[0])
        else:
            port_var.set("")

        # --- REFRESH BUTTON ---
        def refresh_ports():
            new = self.usb.list_ports() if self.usb else []

            combo["values"] = new
            display_combo_a["values"] = new
            display_combo_b["values"] = new

            if self.usb_port in new:
                port_var.set(self.usb_port)
            elif new:
                port_var.set(new[0])
            else:
                port_var.set("")

        tk.Button(frame, text='Obnovit', command=refresh_ports).pack(side='right', padx=6)

        # --- BAUD ---
        tk.Label(dlg, text="Baud (rychlost) — výchozí 115200:").pack(anchor='w', padx=10, pady=(8,0))
        baud_var = tk.StringVar(value=str(self.usb_baud))
        tk.Entry(dlg, textvariable=baud_var, width=10).pack(padx=10, pady=4)

        # --- TIMEOUT ---
        tk.Label(dlg, text="Timeout (s) — výchozí 10.0:").pack(anchor='w', padx=10, pady=(8,0))
        to_var = tk.StringVar(value=str(self.usb_timeout))
        tk.Entry(dlg, textvariable=to_var, width=10).pack(padx=10, pady=4)

        # --- LED PANEL A ---
        ttk.Separator(dlg, orient="horizontal").pack(fill="x", padx=10, pady=8)
        tk.Label(dlg, text="LED displej ID-1",font=("Arial",10,"bold")).pack(anchor='w', padx=10, pady=(12,0))
        display_port_a_var = tk.StringVar(value=self.display_port_a)
        display_combo_a = ttk.Combobox(
            dlg,
            textvariable=display_port_a_var,
            values=ports,
            state="readonly",
            width=20
        )
        display_combo_a.pack(padx=10, pady=4)

        # --- BAUD LED A ---
        tk.Label(dlg, text="Baud (rychlost) — výchozí 115200:").pack(anchor='w', padx=10, pady=(8,0))
        baud_var_A = tk.StringVar(
            value=str(self.display_baud_a)
        )

        tk.Entry(
            dlg,
            textvariable=baud_var_A,
            width=10
        ).pack(padx=10, pady=4)

        # --- LED PANEL B ---
        ttk.Separator(dlg, orient="horizontal").pack(fill="x", padx=10, pady=8)        
        tk.Label(dlg, text="LED displej ID-2",font=("Arial",10,"bold")).pack(anchor='w', padx=10, pady=(12,0))
        display_port_b_var = tk.StringVar(value=self.display_port_b)
        display_combo_b = ttk.Combobox(
            dlg,
            textvariable=display_port_b_var,
            values=ports,
            state="readonly",
            width=20
        )
        display_combo_b.pack(padx=10, pady=4)

        # --- BAUD LED B ---
        tk.Label(dlg, text="Baud (rychlost) — výchozí 115200:").pack(anchor='w', padx=10, pady=(8,0))
        baud_var_B = tk.StringVar(
            value=str(self.display_baud_b)
        )

        tk.Entry(
            dlg,
            textvariable=baud_var_B,
            width=10
        ).pack(padx=10, pady=4)        

        ttk.Separator(dlg, orient="horizontal").pack(fill="x", padx=10, pady=8)

        # --- TEST BUTTONS ---
        test_frame = tk.Frame(dlg)
        test_frame.pack(pady=10)

        tk.Button(
            test_frame,
            text="TEST ID-1",
            width=12,
            command=lambda: test_display(1)
        ).pack(side="left", padx=5)

        tk.Button(
            test_frame,
            text="TEST ID-2",
            width=12,
            command=lambda: test_display(2)
        ).pack(side="left", padx=5) 

        tk.Button(
            test_frame,
            text="SMAZAT",
            width=12,
            command=lambda: test_display(0)
        ).pack(side="left", padx=5)                      

        ttk.Separator(dlg, orient="horizontal").pack(fill="x", padx=10, pady=8)
        # --- OK HANDLER ---
        def on_ok():
            self.usb_port = port_var.get().strip()
            self.display_port_a = (display_port_a_var.get().strip())
            self.display_port_b = (display_port_b_var.get().strip())
            self.update_display_status(1, bool(self.display_port_a))
            self.update_display_status(2, bool(self.display_port_b))            

            try:
                self.usb_baud = int(baud_var.get())
            except:
                self.usb_baud = DEFAULT_USB_BAUD

            try:
                self.display_baud_a = int(baud_var_A.get())
            except:
                self.display_baud_a = DEFAULT_USB_DISPLAY_A_BAUD

            try:
                self.display_baud_b = int(baud_var_B.get())
            except:
                self.display_baud_b = DEFAULT_USB_DISPLAY_B_BAUD                               

            try:
                self.usb_timeout = float(to_var.get())
            except:
                self.usb_timeout = DEFAULT_USB_TIMEOUT

            # save settings
            try:
                spath = os.path.join(os.path.expanduser('~'), '.playoff_settings.json')
                data = {}
                if os.path.exists(spath):
                    try:
                        with open(spath, 'r', encoding='utf-8') as f:
                            data = json.load(f)
                    except:
                        data = {}

                data['usb_port'] = self.usb_port
                data['usb_baud'] = self.usb_baud
                data['usb_timeout'] = self.usb_timeout
                data['display_port_a'] = self.display_port_a
                data['display_port_b'] = self.display_port_b
                data['display_baud_a'] = self.display_baud_a
                data['display_baud_b'] = self.display_baud_b
                data['view_mode'] = self.view_mode

                with open(spath, 'w', encoding='utf-8') as f:
                    json.dump(data, f, ensure_ascii=False, indent=2)
            except:
                pass

            # validate port
            try:
                if self.usb:
                    self.usb.validate_and_set(self.usb_port, self.usb_baud, self.usb_timeout)
                    self.usb.start_reader(self.on_usb_line)
                    self.update_usb_status(True)
            except Exception as e:
                messagebox.showwarning("USB", f"Port nastaven, ale spojení selhalo:\n{e}")
                self.update_usb_status(False)

            try:
                self.usb.disconnect_displays()
                self.usb.connect_displays()

                self.root.after(
                    2500,
                    lambda: self.usb.send_display(1, "TXT:ID-1")
                )
                self.root.after(
                    2600,
                    lambda: self.usb.send_display(2, "TXT:ID-2")
                )                
                self.root.after(
                    7000,
                    lambda: self.usb.send_display(1, "TXT:-------")
                )
                self.root.after(
                    7200,
                    lambda: self.usb.send_display(2, "TXT:-------")
                )
            except:
                pass                

            dlg.destroy()

        def on_cancel():
            dlg.destroy()

        # --- BUTTONS ---
        btnf = tk.Frame(dlg)
        btnf.pack(pady=8)
        tk.Button(btnf, text='OK', width=10, command=on_ok).pack(side='left', padx=6)
        tk.Button(btnf, text='Zrušit', width=10, command=on_cancel).pack(side='left', padx=6)

        dlg.bind('<Return>', lambda e: on_ok())
        dlg.bind('<Escape>', lambda e: on_cancel())
        self.root.wait_window(dlg)


    # --- bracket generation (exact number of teams) ---
    def generate_bracket_with_empty(self, n):
        # create list of n empty slots
        team_list = [""] * int(max(0, n))
        use_pre_round=self.pre_round_enabled
        if use_pre_round:
            pre_round_list = [""] * int(max(0, n))
        else:
            pre_round_list = []   
        self.bracket = Bracket(team_list, pre_round_list=pre_round_list, use_pre_round=use_pre_round)
        # resolve automatic BYE if requested
        if self.odd_behavior == 'auto':
            self._auto_resolve_byes()
        self.redraw()

    def generate_from_entry(self):
        try:
            n = int(self.team_var.get())
            if n < 1:
                raise ValueError('Musí být alespoň 1 tým')
            self.generate_bracket_with_empty(n)
        except Exception:
            messagebox.showerror("Chyba", "Počet týmů není platné číslo.")

    # --- save / load setup ---
    def save_setup(self):
        self._log("SAVE_SETUP CALLED")
        fname = filedialog.asksaveasfilename(defaultextension='.setup', filetypes=[('Playoff setup', '.setup'), ('JSON', '.json')])

        if not fname:
            return

        if self.bracket:
            team_count = self.bracket.team_count
            titles = self.bracket.titles
            pre_titles = self.bracket.pre_titles
        else:
            team_count = 0
            titles = []
            pre_titles = []

        data = {
            'team_count': team_count,
            'odd_behavior': self.odd_behavior,
            'font_scale': self.font_scale,
            'canvas_bg': self.canvas_bg,
            'line_width': self.line_width,
            'bg_path': self.bg_path,
            'lock_edit': self.lock_edit,
            'titles': titles,
            'rounds': [],
            'winner': self.current_winner,
            'enable_timer': self.enable_timer,
            'timer_value': self.timer_value, 
            'timer_start_mode': self.timer_start_mode,
            'pre_round_enabled': self.pre_round_enabled,                       
            # USB fields
            'usb_port': self.usb_port,
            'usb_baud': self.usb_baud,
            'usb_timeout': self.usb_timeout,
            # USB LED panels fields
            'display_port_a': self.display_port_a,
            'display_port_b': self.display_port_b,
            'display_baud_a': self.display_baud_a,
            'display_baud_b': self.display_baud_b,
            # mode (playoff/laps)
            'view_mode': self.view_mode,
            # TEAMS names
            'team_names': self.team_names,
            # THIRD place
            'third_place_enabled': self.third_place_enabled,
            'third_place': self.third_place,
            'third_place_title': self.third_place_title,
            # PRE ROUNDS
            'pre_titles': pre_titles,
            'pre_rounds': [],
            'lap_timer_enabled': self.lap_timer_enabled,
        }
        if (self.bracket and self.pre_round_enabled and self.bracket.pre_rounds):
            data['pre_rounds'] = [
                [
                    {
                        'a': m.a.text,
                        'b': m.b.text
                    }
                    for m in self.bracket.pre_rounds[0]
                ]
            ]
        if self.bracket:
            for r in self.bracket.rounds:
                rd = []
                for m in r:
                    rd.append({'a': m.a.text, 'b': m.b.text})
                data['rounds'].append(rd)
        try:
            with open(fname, 'w', encoding='utf-8') as f:
                json.dump(data, f, ensure_ascii=False, indent=2)
            messagebox.showinfo('Hotovo', f'Soubor byl uložen: {fname}')
        except Exception as e:
            messagebox.showerror('Chyba', str(e))

    def load_setup(self):
        self._log("LOAD setup.json")
        fname = filedialog.askopenfilename(filetypes=[('Playoff setup', '.setup .json')])
        if not fname:
            return
        try:
            with open(fname, 'r', encoding='utf-8') as f:
                data = json.load(f)
        except Exception as e:
            messagebox.showerror('Chyba', f'Nepodařilo se načíst soubor: {e}')
            self._log('Chyba', f'Nepodařilo se načíst soubor: {e}')
            return
        # rebuild bracket with exact count
        n = data.get('team_count', 0)
        self.odd_behavior = data.get('odd_behavior', 'manual')
        self.font_scale = data.get('font_scale', 'medium')
        self.canvas_bg = data.get('canvas_bg', CANVAS_BG_DEFAULT)
        self.line_width = data.get('line_width', 2)
        self.line_width_var.set(self.line_width)
        self.bg_path = data.get('bg_path')
        self.lock_edit = data.get('lock_edit', False)
        self.canvas.config(bg=self.canvas_bg)
        self.enable_timer = data.get('enable_timer', getattr(self, 'enable_timer', True))
        self.timer_value = data.get('timer_value', getattr(self, 'timer_value', '05:00'))
        self.timer_start_mode = data.get('timer_start_mode', 'start')
        self.timer_start_mode_var.set(self.timer_start_mode)
        self.team_names = data.get('team_names', [])
        self.pre_round_enabled = data.get('pre_round_enabled', True)
        self.pre_round_var.set(self.pre_round_enabled)
        self.third_place_enabled = data.get('third_place_enabled', False)
        self.third_place_var.set(self.third_place_enabled)
        self.third_place = data.get('third_place', {"a": "", "b": "", "winner": ""})
        self.third_place_title = data.get('third_place_title', "3. místo")
        self.lap_timer_enabled = data.get('lap_timer_enabled', False)
        self.lap_timer_var.set(self.lap_timer_enabled)
        self.display_port_a = data.get('display_port_a', self.display_port_a)
        self.display_port_b = data.get('display_port_b', self.display_port_b)
        self.display_baud_a = data.get('display_baud_a', self.display_baud_a)
        self.display_baud_b = data.get('display_baud_b', self.display_baud_b)
        self.view_mode = data.get('view_mode', 'playoff')
        self.view_mode_var.set(self.view_mode)
        self.update_view_mode_gui()
        self.update_view_mode_buttons()
        # apply UI lap timer state
        if self.lap_timer_enabled:
            self.lap_label_a.pack(side='left', padx=(10, 5))
            self.lap_label_b.pack(side='left', padx=(0, 20))                
        self.generate_bracket_with_empty(n)

        # --- LOAD PRE ROUND ---
        pre_titles = data.get('pre_titles', [])
        pre_rounds = data.get('pre_rounds', [])

        if self.pre_round_enabled and pre_rounds:
            if not self.bracket.pre_rounds:
                self.bracket._build_pre([""] * n)

            self.bracket.pre_titles = pre_titles if pre_titles else ["Předkolo"]

            for m_idx, mdata in enumerate(pre_rounds[0]):
                if m_idx < len(self.bracket.pre_rounds[0]):
                    self.bracket.pre_rounds[0][m_idx].a.text = mdata.get('a', '')
                    self.bracket.pre_rounds[0][m_idx].b.text = mdata.get('b', '')
        try:
            # ensure timer menu var exists
            self.timer_menu_var.set(self.enable_timer)
        except Exception:
            pass
        # update timer display/visibility
        try:
            self.timer_label.config(text=self.timer_value)
            self.update_timer_visibility()
        except Exception:
            pass

        # rebuild rounds exactly as in setup
        rounds_in = data.get('rounds', [])
        if rounds_in:
            self.bracket.rounds = []
            for rdata in rounds_in:
                round_list = []
                for m in rdata:
                    a = Slot(m.get('a', ''))
                    b = Slot(m.get('b', ''))
                    round_list.append(Match(a, b))
                self.bracket.rounds.append(round_list)

        # load titles
        titles = data.get('titles', [])
        for i, t in enumerate(titles):
            if i < len(self.bracket.titles):
                self.bracket.titles[i] = t
        if self.bracket.rounds:
            if len(self.bracket.rounds[-1]) > 1:
                self.bracket.rounds[-1] = [self.bracket.rounds[-1][0]]

        # load rounds text
        rounds_in = data.get('rounds', [])
        for r_idx, rd in enumerate(rounds_in):
            if r_idx >= len(self.bracket.rounds):
                break
            matches = self.bracket.rounds[r_idx]
            for m_idx, mdata in enumerate(rd):
                if m_idx >= len(matches):
                    break
                matches[m_idx].a.text = mdata.get('a', '')
                matches[m_idx].b.text = mdata.get('b', '')

        # try load bg image if exists
        if self.bg_path and PIL_AVAILABLE and os.path.exists(self.bg_path):
            try:
                self.bg_image = Image.open(self.bg_path).convert('RGBA')
            except Exception:
                self.bg_image = None

        self.current_winner = data.get('winner', '')
        
        # load USB fields if present in setup file
        self.usb_port = data.get('usb_port', self.usb_port)
        self.usb_baud = data.get('usb_baud', self.usb_baud)
        self.usb_timeout = data.get('usb_timeout', self.usb_timeout)
        if self.usb:
            try:
                self.usb.validate_and_set(self.usb_port, self.usb_baud, self.usb_timeout)
                if self.usb_port:
                    self.update_usb_status(True)
                else:
                    self.update_usb_status(False)
            except Exception:
                self.update_usb_status(False)

        self.root.update_idletasks()
        self.root.after(50, self.redraw)
        messagebox.showinfo('Hotovo', 'Soubor byl načten')
        self._log('Hotovo', 'Soubor byl načten')

    # --- Timer methods (MM:SS input, countdown, blinking) ---
    def on_toggle_timer(self):
        self.enable_timer = self.timer_menu_var.get()
        # persist small settings to user home file
        try:
            spath = os.path.join(os.path.expanduser('~'), '.playoff_settings.json')
            data = {}
            if os.path.exists(spath):
                try:
                    with open(spath, 'r', encoding='utf-8') as f:
                        data = json.load(f)
                except Exception:
                    data = {}
            data['enable_timer'] = self.enable_timer
            data['timer_value'] = self.timer_value
            with open(spath, 'w', encoding='utf-8') as f:
                json.dump(data, f, ensure_ascii=False, indent=2)
        except Exception:
            pass
        try:
            self.update_timer_visibility()
        except Exception:
            pass

        self.redraw()

    def on_toggle_lap_timer(self):
        self.lap_timer_enabled = self.lap_timer_var.get()

        # UI toggle
        if self.lap_timer_enabled:
            self.lap_label_a.pack(side='left', padx=(10, 5))
            self.lap_label_b.pack(side='left', padx=(0, 20))
        else:
            self.lap_label_a.pack_forget()
            self.lap_label_b.pack_forget()

        # save to file
        try:
            spath = os.path.join(os.path.expanduser('~'), '.playoff_settings.json')
            data = {}

            if os.path.exists(spath):
                try:
                    with open(spath, 'r', encoding='utf-8') as f:
                        data = json.load(f)
                except Exception:
                    data = {}

            data['lap_timer_enabled'] = self.lap_timer_enabled

            with open(spath, 'w', encoding='utf-8') as f:
                json.dump(data, f, ensure_ascii=False, indent=2)

        except Exception:
            pass

    def update_timer_visibility(self):
        try:
            if getattr(self, 'timer_window', None) is None:
                return
            if self.enable_timer:
                self.canvas.itemconfigure(self.timer_window, state='normal')
            else:
                self.canvas.itemconfigure(self.timer_window, state='hidden')
        except Exception:
            try:
                if self.enable_timer:
                    self.timer_label.place(relx=0.98, rely=0.98, anchor='se')
                else:
                    self.timer_label.place_forget()
            except Exception:
                pass

    def update_timer_display(self):
        try:
            self.timer_label.config(text=self.timer_value, bg='black', fg='white')
        except Exception:
            pass

    def on_timer_right_click(self, event=None):
        class WideEntryDialog(simpledialog._QueryString):
            def body(self, master):
                super().body(master)
                self.entry.config(width=15)
                return self.entry

        d = WideEntryDialog(
            title='Nastavení odpočtu',
            prompt='Zadejte čas ve formátu MM:SS',
            initialvalue=getattr(self, 'timer_value', '05:00'),
            parent=self.root
        )

        val = d.result
        if val is None:
            return
        
        if self.validate_time_format(val):
            self.timer_value = val
            self.timer_label.config(text=self.timer_value)
            try:
                spath = os.path.join(os.path.expanduser('~'), '.playoff_settings.json')
                data = {}
                if os.path.exists(spath):
                    with open(spath, 'r', encoding='utf-8') as f:
                        data = json.load(f)
                data['timer_value'] = self.timer_value
                with open(spath, 'w', encoding='utf-8') as f:
                    json.dump(data, f, ensure_ascii=False, indent=2)
            except Exception:
                pass
        else:
            messagebox.showerror('Chyba', 'Neplatný formát času. Použij MM:SS (např. 03:30).')

    def validate_time_format(self, text):
        try:
            parts = text.split(':')
            if len(parts) != 2:
                return False
            m = int(parts[0]); s = int(parts[1])
            if m < 0 or s < 0 or s >= 60:
                return False
            return True
        except Exception:
            return False

    def time_to_seconds(self, t):
        parts = t.split(':')
        if len(parts) != 2:
            return 0
        return int(parts[0]) * 60 + int(parts[1])

    def seconds_to_time(self, sec):
        m = sec // 60
        s = sec % 60
        return f"{m:02d}:{s:02d}"

    def start_countdown(self):
        try:
            # stop blinking if active
            self.stop_blinking()
        except Exception:
            pass
        try:
            if getattr(self, 'countdown_after_id', None):
                try:
                    self.root.after_cancel(self.countdown_after_id)
                except Exception:
                    pass
                self.countdown_after_id = None
        except Exception:
            self.countdown_after_id = None
        try:
            self.current_seconds = self.time_to_seconds(self.timer_value)
            self.timer_label.config(text=self.seconds_to_time(self.current_seconds))
            self.timer_running = True
            # schedule tick
            self.countdown_after_id = self.root.after(1000, self.countdown_tick)
        except Exception:
            pass

    def countdown_tick(self):
        try:
            if not getattr(self, 'timer_running', False):
                return
            if self.current_seconds <= 0:
                self.timer_running = False
                self.lap_running_a = False
                self.lap_running_b = False
                if self.lap_after_id:
                    try:
                        self.root.after_cancel(self.lap_after_id)
                    except:
                        pass
                self.start_blinking()
                return
            self.current_seconds -= 1
            try:
                self.timer_label.config(text=self.seconds_to_time(self.current_seconds))
            except Exception:
                pass
            self.countdown_after_id = self.root.after(1000, self.countdown_tick)
        except Exception:
            pass

    def start_blinking(self):
        try:
            self.timer_blink = True
            self.blink_state = False
            # kickoff blink loop
            self._blink_step()
        except Exception:
            pass

    def _blink_step(self):
        try:
            if not getattr(self, 'timer_blink', False):
                return
            self.blink_state = not getattr(self, 'blink_state', False)
            if self.blink_state:
                self.timer_label.config(bg='red', fg='white')
            else:
                self.timer_label.config(bg='white', fg='red')
            # schedule next
            self.blink_after_id = self.root.after(500, self._blink_step)
        except Exception:
            pass

    def stop_blinking(self):
        try:
            self.timer_blink = False
            if getattr(self, 'blink_after_id', None):
                try:
                    self.root.after_cancel(self.blink_after_id)
                except Exception:
                    pass
                self.blink_after_id = None
            self.timer_label.config(bg='black', fg='white')
        except Exception:
            pass


    def _auto_resolve_byes(self):
        """Automatic BYE teams"""
        rounds = self.bracket.rounds
        last_round_index = len(rounds) - 1  # poslední kolo je Vítěz

        for r_idx in range(len(rounds) - 1):
            if r_idx == last_round_index:
                continue

            matches = rounds[r_idx]

            for m_idx, match in enumerate(matches):

                a = match.a.text.strip()
                b = match.b.text.strip()

                if (a and not b) or (b and not a):
                    winner = a if a else b

                    next_index = m_idx // 2
                    next_match = rounds[r_idx + 1][next_index]
                    side = 'a' if (m_idx % 2 == 0) else 'b'

                    if side == 'a':
                        next_match.a.text = winner
                    else:
                        next_match.b.text = winner


    # --- editing title (wide dialog) ---                       
    def edit_title(self, r_idx):
        if self.lock_edit:
            return

        dlg = tk.Toplevel(self.root)
        dlg.title('Změnit nadpis')
        dlg.transient(self.root)
        dlg.grab_set()

        tk.Label(dlg, text='Nadpis:').pack(padx=10, pady=(10, 4))

        ent = tk.Entry(dlg, width=40)
        current = self.bracket.titles[r_idx] if r_idx < len(self.bracket.titles) else ""
        ent.insert(0, current)
        ent.pack(padx=10, pady=4)
        ent.focus_set()

        def on_ok():
            new_title = ent.get().strip()
            if r_idx < len(self.bracket.titles):
                self.bracket.titles[r_idx] = new_title
            dlg.destroy()
            self.redraw()

        def on_cancel():
            dlg.destroy()

        btns = tk.Frame(dlg)
        btns.pack(pady=10)
        tk.Button(btns, text="OK", width=10, command=on_ok).pack(side="left", padx=6)
        tk.Button(btns, text="Zrušit", width=10, command=on_cancel).pack(side="left", padx=6)

        dlg.bind("<Return>", lambda e: on_ok())
        dlg.bind("<Escape>", lambda e: on_cancel())

        self.root.wait_window(dlg)


    # --- editing UI (wide dialog) ---
    def edit_slot_dialog(self, r_idx, m_idx, side):
        if self.lock_edit:
            return
        m = self.bracket.rounds[r_idx][m_idx]
        slot = m.a if side == 'a' else m.b
        # create custom dialog
        dlg = tk.Toplevel(self.root)
        dlg.title('Zadej tým')
        dlg.transient(self.root)
        dlg.grab_set()
        w = 480
        h = 120
        x = (dlg.winfo_screenwidth() - w)//2
        y = (dlg.winfo_screenheight() - h)//2
        dlg.geometry(f'{w}x{h}+{x}+{y}')
        tk.Label(dlg, text='Zadej číslo nebo název týmu:').pack(anchor='w', padx=10, pady=(10,0))
        ent = tk.Entry(dlg, width=60)
        ent.pack(padx=10, pady=8)
        ent.insert(0, slot.text)
        ent.focus_set()
        def on_ok():
            slot.text = ent.get()
            dlg.destroy()
            self.redraw()
        def on_cancel():
            dlg.destroy()
        btnf = tk.Frame(dlg)
        btnf.pack(pady=6)
        tk.Button(btnf, text='OK', command=on_ok).pack(side='left', padx=8)
        tk.Button(btnf, text='Zrušit', command=on_cancel).pack(side='left')
        dlg.bind('<Return>', lambda e: on_ok())
        dlg.bind('<Escape>', lambda e: on_cancel())
        self.root.wait_window(dlg)

    def edit_winner_dialog(self):
        if self.lock_edit:
            return
        dlg = tk.Toplevel(self.root)
        dlg.title("Zadat vítěze")
        dlg.transient(self.root)
        dlg.grab_set()

        tk.Label(dlg, text="Jméno / číslo vítěze:").pack(padx=10, pady=(10, 4))
        ent = tk.Entry(dlg, width=40)
        ent.pack(padx=10, pady=6)
        ent.insert(0, self.current_winner)
        ent.focus_set()

        def on_ok():
            new_val = ent.get().strip()

            last_round = len(self.bracket.rounds) - 1
            winner_match = self.bracket.rounds[last_round][0]

            winner_match.a.text = new_val
            winner_match.b.text = ""

            self.current_winner = new_val
            self.update_third_place_from_semifinal()
            dlg.destroy()
            self.redraw()

        def on_cancel():
            dlg.destroy()

        btn = tk.Frame(dlg)
        btn.pack(pady=10)
        tk.Button(btn, text="OK", command=on_ok).pack(side="left", padx=6)
        tk.Button(btn, text="Zrušit", command=on_cancel).pack(side="left", padx=6)

        dlg.bind("<Return>", lambda e: on_ok())
        dlg.bind("<Escape>", lambda e: on_cancel())

        self.root.wait_window(dlg)

    # --- promote (right-click) ---
    def promote(self, r_idx, m_idx, side):
        match = self.bracket.rounds[r_idx][m_idx]
        winner = match.a.text.strip() if side == 'a' else match.b.text.strip()

        if not winner:
            messagebox.showwarning('Upozornění', 'Pole je prázdné — nejdřív vyplň tým.')
            return

        if r_idx + 1 < len(self.bracket.rounds):
            next_index = m_idx // 2
            next_match = self.bracket.rounds[r_idx + 1][next_index]
            next_side = 'a' if (m_idx % 2 == 0) else 'b'
            target = next_match.a if next_side == 'a' else next_match.b

            if target.text:
                if not messagebox.askyesno('Přepsat?', 'V cílovém poli už něco je. Přepsat?'):
                    return

            target.text = winner
            self.update_third_place_from_semifinal()
            self.redraw()
            return

        winner_round_index = len(self.bracket.rounds) - 1   
        winner_match = self.bracket.rounds[winner_round_index][0]

        winner_match.a.text = winner
        winner_match.b.text = ""  

        self.update_third_place_from_semifinal()
        self.redraw()
        return

    def promote_third_place(self, side):
        val = self.third_place[side].strip()
        if not val:
            return

        if self.third_place["winner"]:
            if not messagebox.askyesno("Přepsat?", "Vítěz pro 3. místo už existuje. Přepsat?"):
                return

        self.third_place["winner"] = val
        self.redraw()    

    def edit_third_place_title(self):
        if self.lock_edit:
            return

        dlg = tk.Toplevel(self.root)
        dlg.title("Nadpis 3. místa")

        ent = tk.Entry(dlg, width=30)
        ent.pack(padx=10, pady=10)
        ent.insert(0, self.third_place_title)
        ent.focus()

        def ok():
            self.third_place_title = ent.get()
            dlg.destroy()
            self.redraw()

        tk.Button(dlg, text="OK", command=ok).pack(pady=5)
        dlg.bind("<Return>", lambda e: ok())            

    # --- reset vs clear ---
    def reset_values(self):
        if not self.bracket:
            return
        # --- NORMAL ROUNDS ---
        for r in self.bracket.rounds:
            for m in r:
                m.a.text = ''
                m.b.text = ''
        # --- PRE ROUND ---
        if self.pre_round_enabled and self.bracket.pre_rounds:
            for r in self.bracket.pre_rounds:
                for m in r:
                    m.a.text = ''
                    m.b.text = ''
        # --- WINNER ---
        self.current_winner = ""
        # --- THIRD PLACE ---
        self.third_place = {"a": "", "b": "", "winner": ""}
        self.redraw()

    def clear_all(self):
        # clear everything: remove bracket and background; user must generate again
        self.bracket = None
        self.canvas.delete("all")
        self.bg_path = None
        self.bg_image = None
        self.bg_tk = None
        self.canvas_bg = CANVAS_BG_DEFAULT
        self.canvas.config(bg=self.canvas_bg)
        self.team_var.set('0')
        self.canvas.delete('all')

    # --- background functions ---
    def load_bg_image(self):
        if not PIL_AVAILABLE:
            messagebox.showerror('Chyba python Pillow', 'Pillow není nainstalován. Nainstaluj: pip install pillow')
            return
        path = filedialog.askopenfilename(title='Vyber obrázek', filetypes=[('Images','*.png;*.jpg;*.jpeg;*.bmp;*.gif')])
        if not path:
            return
        try:
            img = Image.open(path).convert('RGBA')
            self.bg_path = path
            self.bg_image = img
            self.bg_tk = None
            messagebox.showinfo('Načteno', f'Načteno: {os.path.basename(path)}')
            self.redraw()
        except Exception as e:
            messagebox.showerror('Chyba', str(e))

    def remove_bg(self):
        self.bg_path = None
        self.bg_image = None
        self.bg_tk = None
        self.redraw()
        messagebox.showinfo('Hotovo', 'Pozadí bylo odstraněno')

    # --- help ---
    def show_help(self):
        dlg = tk.Toplevel(self.root)
        dlg.title("Nápověda – Playoff generátor")
        dlg.transient(self.root)
        dlg.grab_set()
        dlg.geometry("800x600")

        frame = tk.Frame(dlg)
        frame.pack(fill="both", expand=True, padx=10, pady=10)

        scrollbar = tk.Scrollbar(frame)
        scrollbar.pack(side="right", fill="y")

        text = tk.Text(
            frame,
            wrap="word",
            yscrollcommand=scrollbar.set,
            font=("Arial", 11)
        )
        text.pack(side="left", fill="both", expand=True)

        scrollbar.config(command=text.yview)

        help_text = (
            "NÁPOVĚDA – PLAYOFF GENERÁTOR\n"
            "Autor: Martin Pihrt © www.pihrt.com\n\n"

            "=== ZÁKLADNÍ OVLÁDÁNÍ ===\n"
            "- Počet týmů: Nastavení → Počet týmů max 24\n"
            "- Generovat prázdné týmy: Nastavení → Generovat týmy\n"
            "- Editace týmu: Levé tlačítko myši na buňku\n"
            "- Postup do dalšího kola: Pravé tlačítko myši na tým\n"
            "- Zamknout editaci: Nastavení → Zamknout editaci týmů\n"
            "- Smazat obsah: Vymaže pouze názvy týmů\n"
            "- Vymazat vše: Odstraní pavouka i pozadí\n\n"

            "=== KOLO A TITULKY ===\n"
            "- Kliknutím na nadpis kola lze změnit jeho název\n"
            "- Poslední sloupec je vždy VÍTĚZ\n\n"

            "=== POJMENOVÁNÍ TÝMŮ ===\n"
            "Nastavení → Pojmenování týmů\n"
            "- Sloupce: ID týmu / Popis týmu\n"
            "- Neomezený počet řádků\n"
            "- Ruční editace\n"
            "- Import z Excelu\n"
            "- Export do Excelu\n"
            "- Tlačítko Smazat vše\n"
            "- Data se ukládají do souboru spolu s pavoukem\n\n"

            "=== TABULKA VPRAVO OD PAVOUKA ===\n"
            "- Automaticky se generuje z Kola 1\n"
            "- Zobrazuje pouze ID, které existují v pojmenování týmů\n"
            "- Řazení je číselně vzestupně\n"
            "- Velikost písma odpovídá nastavení velikosti pavouka\n\n"

            "=== LICHÝ POČET TÝMŮ ===\n"
            "Nastavení → Chování při lichém počtu vítězů\n"
            "- Automatický BYE\n"
            "- Ruční postup\n"
            "- Čekající hráč\n\n"

            "=== VZHLED ===\n"
            "Nastavení → Velikost písma\n"
            "- Malé / Střední / Velké\n\n"
            "Nastavení → Tloušťka čar\n"
            "- Normální / Silné\n\n"
            "Nastavení → Barva pozadí\n"
            "Nastavení → Načíst pozadí\n"
            "Nastavení → Smazat pozadí\n\n"

            "=== USB SEMAFOR ===\n"
            "Nastavení → USB nastavení\n"
            "- Výběr COM portu\n"
            "- Nastavení Baud rate (výchozí 9600)\n"
            "- Timeout odpovědi (výchozí 10 s)\n\n"
            "Tlačítko START:\n"
            "- Odešle text 'start' do zařízení\n"
            "- Očekává zpět text 'ok'\n"
            "- Stav je zobrazen v horní liště\n\n"

            "=== ODPOČET ===\n"
            "Nastavení → Povolit odpočet\n"
            "- Pod vítězem se zobrazí časovač MM:SS\n"
            "- Pravým tlačítkem myši lze změnit čas\n\n"
            "Režim spuštění odpočtu:\n"
            "- Spustit odpočet ihned (po START)\n"
            "- Spustit odpočet až po semaforu (OK)\n\n"

            "=== PDF EXPORT ===\n"
            "Nastavení → Export do PDF\n"
            "- První stránka: pavouk + vítěz + datum a čas exportu\n"
            "- Druhá stránka: tabulka pojmenování týmů\n"
            "- Automatické stránkování při dlouhé tabulce\n\n"

            "=== PROJEKTOROVÝ REŽIM ===\n"
            "Nastavení → Celá obrazovka ZAP/VYP\n"
            "- Přepne aplikaci na fullscreen\n"
            "- Klávesa ESC režim ukončí\n\n"

            "=== UKLÁDÁNÍ A NAČÍTÁNÍ ===\n"
            "Nastavení → Uložit do souboru\n"
            "- Uloží kompletní stav pavouka, pozadí, USB, odpočet i pojmenování týmů\n\n"
            "Nastavení → Načíst ze souboru\n"
            "- Obnoví veškerý uložený obsah\n\n"

            "=== AKTUALIZACE ===\n"
            "Nastavení → Kontrola aktualizace\n"
            "- Ověří novou verzi programu na internetu\n\n"

            "=== ČAS A DATUM ===\n"
            "- V horní liště se zobrazuje aktuální datum a čas v reálném čase\n"
        )

        text.insert("1.0", help_text)
        text.config(state="disabled")

        btn = tk.Button(dlg, text="Zavřít", command=dlg.destroy)
        btn.pack(pady=8)

        dlg.bind("<Escape>", lambda e: dlg.destroy())
        self.root.wait_window(dlg)

    # --- fullscreen ---
    def toggle_projector(self):
        self.projector_mode = self.fullscreen_var.get()
        # aktivace fullscreen
        self.root.attributes('-fullscreen', self.projector_mode)
        self.root.after(50, self.redraw)

    def exit_fullscreen(self):
        self.projector_mode = False
        self.fullscreen_var.set(False)
        self.root.attributes('-fullscreen', False)
        self.root.after(50, self.redraw)

    def build_team_lookup_from_round1(self):
        if not self.bracket or not self.bracket.rounds:
            return []

        round_index = 0

        ids = []
        for m in self.bracket.rounds[round_index]:
            a = m.a.text.strip()
            b = m.b.text.strip()
            if a:
                ids.append(a)
            if b:
                ids.append(b)

        lookup = {str(x.get("id", "")).strip(): x.get("desc", "") for x in self.team_names}

        result = []
        for tid in ids:
            if tid in lookup:
                result.append((tid, lookup[tid]))

        def sort_key(x):
            try:
                return int(x[0])
            except Exception:
                return 10**9

        result.sort(key=sort_key)
        return result

    # --- playoff mode ---
    def redraw(self):
        self.canvas.delete("all")
        if self.view_mode == "laps":
            self.draw_laps()
            return

        self.rect_items.clear()
        self.text_items.clear()
        self.title_items.clear()
        self.line_items.clear()

        # --- BACKGROUND IMAGE ---
        if self.bg_image and PIL_AVAILABLE:
            try:
                cw = self.canvas.winfo_width()
                ch = self.canvas.winfo_height()

                if cw > 1 and ch > 1:
                    # scale image to canvas size
                    img = self.bg_image.resize((cw, ch), Image.LANCZOS)
                    self.bg_tk = ImageTk.PhotoImage(img)
                    self.canvas.create_image(0, 0, image=self.bg_tk, anchor="nw")
            except Exception as e:
                self._log("BACKGROUND ERROR:", e)

        if not self.bracket:
            return

        width = self.root.winfo_screenwidth() if self.projector_mode else max(800, self.canvas.winfo_width())
        height = self.root.winfo_screenheight() if self.projector_mode else max(600, self.canvas.winfo_height())
        self.canvas.config(width=width, height=height, bg=self.canvas_bg)

        rounds = self.bracket.rounds
        pre_rounds = self.bracket.pre_rounds if self.pre_round_enabled else []
        rounds_count = len(rounds)
        last_round = rounds_count - 1
        final_real_round = last_round - 1

        # --- font sizes ---
        if self.font_scale == 'large':
            cell_font_size = 28
        elif self.font_scale == 'small':
            cell_font_size = 12
        else:
            cell_font_size = 14

        cell_font = tkfont.Font(family="Arial", size=cell_font_size)

        if self.font_scale == 'large':
            title_font_size = 13
        elif self.font_scale == 'medium':
            title_font_size = 11
        else:
            title_font_size = 8

        title_font = ("Arial", title_font_size, "bold")

        # --- column widths ---
        col_widths = []
        padding = 20
        min_w = 60
        max_w = 220

        for r_idx, matches in enumerate(rounds):
            if r_idx == last_round:
                winner_match = rounds[last_round][0]
                winner_text = winner_match.a.text.strip() or winner_match.b.text.strip() or self.current_winner
                text_px = cell_font.measure(winner_text)
                col_widths.append(max(min_w, min(max_w, text_px + padding)))
                continue

            max_px = 0
            for m in matches:
                max_px = max(max_px, cell_font.measure(m.a.text.strip()))
                max_px = max(max_px, cell_font.measure(m.b.text.strip()))
            col_widths.append(max(min_w, min(max_w, max_px + padding)))

        margin_x = 40
        margin_y = 40
        h_gap = 70 
        v_gap = 10

        box_h = 40
        per_match_h = box_h * 2 + 8
        initial_matches = len(rounds[0])

        total_h = initial_matches * per_match_h + (initial_matches - 1) * v_gap + 2 * margin_y
        if total_h > height:
            scale = height / total_h
            scale = max(0.25, scale)
            box_h = int(box_h * scale)
            v_gap = max(3, int(v_gap * scale))
            per_match_h = box_h * 2 + 8

        col_x_positions = []
        x = margin_x

        # --- PRE ROUND COLUMN ---
        if self.pre_round_enabled and self.bracket.pre_rounds:
            pre_w = col_widths[0] 
            col_x_positions.append(x)
            x += pre_w + h_gap

        # --- NORMAL ROUNDS ---
        for w in col_widths:
            col_x_positions.append(x)
            x += w + h_gap

        final_centers = []
        semi_losers_centers = []

        if self.pre_round_enabled and self.bracket.pre_rounds:

            pre_matches = self.bracket.pre_rounds[0]
            col_x = col_x_positions[0]
            box_w = col_widths[0]

            title_id = self.canvas.create_text(
                col_x + box_w/2,
                margin_y - 10,
                text=self.bracket.pre_titles[0] if self.bracket.pre_titles else "Předkolo",
                font=title_font,
                fill=TITLE_COLOR,
                width=box_w + 60,
                justify="center",
                anchor="n"                
            )

            if not self.lock_edit:
                self.canvas.tag_bind(title_id, '<Button-1>',
                                     lambda e: self.edit_pre_title())

            matches_count = len(pre_matches)
            total_col_h = matches_count * (box_h * 2 + 8) + (matches_count - 1) * v_gap
            start_y = max(margin_y + title_font_size + 10,
                          (height - total_col_h) // 2)

            for m_idx, match in enumerate(pre_matches):

                top_y = start_y + m_idx * ((box_h * 2 + 8) + v_gap)

                x1 = col_x
                y1 = top_y
                x2 = x1 + box_w
                y2 = y1 + box_h * 2 + 8

                self.canvas.create_rectangle(
                    x1, y1, x2, y2,
                    fill=BOX_FILL,
                    outline=BOX_OUTLINE,
                    width=self.line_width
                )

                self.canvas.create_line(
                    x1, y1 + box_h + 4,
                    x2, y1 + box_h + 4,
                    fill=BOX_OUTLINE,
                    width=max(1, self.line_width - 1)
                )

                if not match.a.text.strip():
                    self.canvas.create_rectangle(x1, y1, x2, y1 + box_h,
                                                 fill=WINNER_FILL, outline="", width=0)

                if not match.b.text.strip():
                    self.canvas.create_rectangle(x1, y1 + box_h + 8, x2, y2,
                                                 fill=WINNER_FILL, outline="", width=0)

                self.canvas.create_text(
                    (x1 + x2)/2,
                    y1 + box_h/2,
                    text=match.a.text,
                    font=("Arial", cell_font_size)
                )

                self.canvas.create_text(
                    (x1 + x2)/2,
                    y1 + box_h + 8 + box_h/2,
                    text=match.b.text,
                    font=("Arial", cell_font_size)
                )

                # HITBOXES
                hit_a = self.canvas.create_rectangle(x1, y1, x2, y1 + box_h,
                                                     fill="", outline="")
                hit_b = self.canvas.create_rectangle(x1, y1 + box_h + 8, x2, y2,
                                                     fill="", outline="")

                if not self.lock_edit:
                    self.canvas.tag_bind(hit_a, '<Button-1>',
                                         lambda e, mm=m_idx: self.edit_pre_slot(mm, 'a'))
                    self.canvas.tag_bind(hit_b, '<Button-1>',
                                         lambda e, mm=m_idx: self.edit_pre_slot(mm, 'b'))                

        offset = 1 if (self.pre_round_enabled and self.bracket.pre_rounds) else 0
        for r_idx, matches in enumerate(rounds):
            col_x = col_x_positions[r_idx + offset]
            box_w = col_widths[r_idx]

            title_id = self.canvas.create_text(
                col_x + box_w/2,
                margin_y - 10,
                text=self.bracket.titles[r_idx],
                font=title_font,
                fill=TITLE_COLOR,
                width=box_w + 60,
                justify="center",
                anchor="n"
            )
            self.canvas.tag_bind(title_id, '<Button-1>', lambda e, rr=r_idx: self.edit_title(rr))

            matches_count = len(matches)
            total_col_h = matches_count * (box_h * 2 + 8) + (matches_count - 1) * v_gap
            start_y = max(margin_y + title_font_size + 10,
                          (height - total_col_h) // 2)

            finalists = set()

            try:
                final_match = rounds[final_real_round + 1][0]
                fa = final_match.a.text.strip()
                fb = final_match.b.text.strip()

                if fa and fb:
                    finalists = {fa, fb}
            except:
                pass

            for m_idx, match in enumerate(matches):

                if r_idx == last_round and len(matches) == 1:
                    continue

                top_y = start_y + m_idx * ((box_h * 2 + 8) + v_gap)

                match_x1 = col_x
                match_y1 = top_y
                match_x2 = match_x1 + box_w
                match_y2 = match_y1 + box_h * 2 + 8

                a_x1, a_y1, a_x2, a_y2 = match_x1, match_y1, match_x2, match_y1 + box_h
                b_x1, b_y1, b_x2, b_y2 = match_x1, a_y2 + 8, match_x2, match_y2

                rect_match = self.canvas.create_rectangle(
                    match_x1, match_y1, match_x2, match_y2,
                    fill=BOX_FILL, outline=BOX_OUTLINE, width=self.line_width
                )

                self.canvas.create_line(
                    a_x1, a_y2 + 4,
                    a_x2, a_y2 + 4,
                    fill=BOX_OUTLINE,
                    width=max(1, self.line_width - 1)
                )

                is_winner_a = (match.a.text.strip() == self.current_winner.strip())
                is_winner_b = (match.b.text.strip() == self.current_winner.strip())

                if is_winner_a:
                    self.canvas.create_rectangle(a_x1, a_y1, a_x2, a_y2, fill=WINNER_FILL, outline="", width=0)
                if is_winner_b:
                    self.canvas.create_rectangle(b_x1, b_y1, b_x2, b_y2, fill=WINNER_FILL, outline="", width=0)

                txt_a = self.canvas.create_text((a_x1+a_x2)/2, (a_y1+a_y2)/2,
                                                text=match.a.text, font=("Arial", cell_font_size))
                txt_b = self.canvas.create_text((b_x1+b_x2)/2, (b_y1+b_y2)/2,
                                                text=match.b.text, font=("Arial", cell_font_size))

                # HITBOXES MUST LAST
                hit_a = self.canvas.create_rectangle(a_x1, a_y1, a_x2, a_y2, fill="", outline="")
                hit_b = self.canvas.create_rectangle(b_x1, b_y1, b_x2, b_y2, fill="", outline="")

                if not self.lock_edit:
                    self.canvas.tag_bind(hit_a, '<Button-1>', lambda e, rr=r_idx, mm=m_idx: self.edit_slot_dialog(rr, mm, 'a'))
                    self.canvas.tag_bind(hit_b, '<Button-1>', lambda e, rr=r_idx, mm=m_idx: self.edit_slot_dialog(rr, mm, 'b'))
                    self.canvas.tag_bind(hit_a, '<Button-3>', lambda e, rr=r_idx, mm=m_idx: self.promote(rr, mm, 'a'))
                    self.canvas.tag_bind(hit_b, '<Button-3>', lambda e, rr=r_idx, mm=m_idx: self.promote(rr, mm, 'b'))

                if r_idx + 1 < rounds_count:
                    cx = a_x2
                    cy = (a_y1 + b_y2) / 2

                    next_col_x = col_x_positions[r_idx + 1 + offset]
                    next_idx = m_idx // 2
                    nm = len(rounds[r_idx + 1])
                    total_h_next = nm * (box_h * 2 + 8) + (nm - 1) * v_gap
                    start_y_next = max(margin_y + title_font_size + 10,
                                       (height - total_h_next) // 2)
                    ny = start_y_next + next_idx * ((box_h * 2 + 8) + v_gap) + box_h

                    self.canvas.create_line(cx, cy, next_col_x, ny,
                                            width=self.line_width, fill=LINE_COLOR, smooth=True)

                if r_idx == final_real_round:
                    final_centers.append(((a_x2), (a_y1 + b_y2) / 2))

                if r_idx == last_round - 2:
                    final_match = rounds[last_round - 1][0]
                    if m_idx == 0:
                        finalist = final_match.a.text.strip()
                    else:
                        finalist = final_match.b.text.strip()
                    if match.a.text.strip() and match.a.text.strip() != finalist:
                        semi_losers_centers.append((a_x2, (a_y1 + a_y2) / 2))
                    if match.b.text.strip() and match.b.text.strip() != finalist:
                        semi_losers_centers.append((b_x2, (b_y1 + b_y2) / 2))

        # --- Winner box ---
        winner_match = rounds[last_round][0]
        winner_text = winner_match.a.text.strip() or winner_match.b.text.strip() or self.current_winner

        text_width = cell_font.measure(winner_text) if winner_text else 0
        win_w = max(text_width + 60, col_widths[last_round] + 40)
        win_h = box_h * 2

        col_x = col_x_positions[last_round + offset]
        win_x_center = col_x + col_widths[last_round] / 2

        win_x1 = win_x_center - win_w/2
        win_x2 = win_x_center + win_w/2
        win_y1 = (height // 2) - win_h//2
        win_y2 = win_y1 + win_h

        self.canvas.create_rectangle(
            win_x1, win_y1, win_x2, win_y2,
            fill=BOX_FILL, outline=BOX_OUTLINE, width=self.line_width+1
        )

        self.canvas.create_text(
            (win_x1+win_x2)/2, (win_y1+win_y2)/2,
            text=winner_text,
            font=("Arial", cell_font_size*2, "bold")
        )

        # --- HITBOX WINNER ---
        hit_winner = self.canvas.create_rectangle(
            win_x1, win_y1, win_x2, win_y2,
            fill="", outline=""
        )

        if not self.lock_edit:
            self.canvas.tag_bind(hit_winner, '<Button-1>',
                                 lambda e: self.edit_winner_dialog())

        # one line between the final and the winner = we will use the AVERAGE of both centers
        if final_centers:
            avg_x = sum(p[0] for p in final_centers) / len(final_centers)
            avg_y = sum(p[1] for p in final_centers) / len(final_centers)
            self.line_items.append((avg_x, avg_y, win_x1, (win_y1 + win_y2) / 2, self.line_width, LINE_COLOR))

        # === TABLE WITH TEAMS NAMES ===
        table_drawn = False
        table_bottom_y = 0
        table_right_x = 0
        try:
            table_data = self.build_team_lookup_from_round1()
            if table_data:
                table_x1 = win_x2 + 20
                table_x2 = width - 20

                if table_x2 - table_x1 > 200:
                    table_y = margin_y - 10
                    table_font_size = min(cell_font_size - 1, 18)
                    row_h = max(26, table_font_size + 10)

                    col1_w = 50
                    col2_w = table_x2 - table_x1 - col1_w - 10

                    self.canvas.create_rectangle(
                        table_x1, table_y,
                        table_x2, table_y + row_h,
                        fill="#dddddd", outline=BOX_OUTLINE, width=1
                    )

                    self.canvas.create_text(
                        table_x1 + col1_w/2, table_y + row_h/2,
                        text="ID", font=("Arial", min(16, table_font_size), "bold")
                    )

                    col_title = self.bracket.titles[0] if self.bracket.titles else "Popis"
                    self.canvas.create_text(
                        table_x1 + col1_w + col2_w/2 + 5, table_y + row_h/2,
                        text=col_title, font=("Arial", min(16, table_font_size), "bold")
                    )

                    y = table_y + row_h

                    for row_index, (tid, name) in enumerate(table_data):
                        if row_index % 2 == 0:
                            row_fill = "#ffffff"
                        else:
                            row_fill = "#f2f2f2"

                        temp_id = self.canvas.create_text(
                            0, 0,
                            text=name,
                            font=("Arial", table_font_size),
                            width=col2_w - 16
                        )

                        bbox = self.canvas.bbox(temp_id)
                        text_height = bbox[3] - bbox[1] if bbox else table_font_size
                        self.canvas.delete(temp_id)

                        row_h = max(26, text_height + 12)

                        self.canvas.create_rectangle(
                            table_x1, y,
                            table_x2, y + row_h,
                            fill=row_fill,
                            outline=BOX_OUTLINE,
                            width=1
                        )

                        self.canvas.create_line(
                            table_x1 + col1_w,
                            y,
                            table_x1 + col1_w,
                            y + row_h,
                            fill=BOX_OUTLINE,
                            width=1
                        )

                        # ID
                        self.canvas.create_text(
                            table_x1 + col1_w / 2,
                            y + row_h / 2,
                            text=str(tid),
                            font=("Arial", table_font_size)
                        )

                        # LABEL
                        self.canvas.create_text(
                            table_x1 + col1_w + 8,
                            y + row_h / 2,
                            text=name,
                            font=("Arial", table_font_size),
                            anchor="w",
                            width=col2_w - 16,
                            justify="left"
                        )

                        y += row_h

                    table_drawn = True
                    table_bottom_y = y
                    table_right_x = table_x2

        except Exception as e:
            self._log("TEAM TABLE ERROR:", e)

        # === 3RD PLACE ===
        if self.third_place_enabled:
            semi_col_index = final_real_round + offset
            semi_col_x = col_x_positions[semi_col_index]
            base_x = semi_col_x

            third_offset_y = 100
            base_y = win_y2 + third_offset_y

            # small boxes A/B
            box_w = col_widths[final_real_round] if col_widths else 120
            box_h_small = box_h
            gap = 6

            # --- BIG WINNER BOX ---
            winner_text_tp = self.third_place["winner"]
            text_width_tp = cell_font.measure(winner_text_tp) if winner_text_tp else 0

            winner_w = max(text_width_tp + 60, col_widths[last_round] + 40)
            winner_h = box_h * 2

            win_x = win_x1

            # TITLE
            title_id = self.canvas.create_text(
                base_x + 60,
                base_y - 25,
                text=self.third_place_title,
                font=title_font
            )

            if not self.lock_edit:
                self.canvas.tag_bind(title_id, "<Button-1>", lambda e: self.edit_third_place_title())

            # --- LEFT MATCH ---
            a_y1 = base_y
            b_y1 = a_y1 + box_h_small + gap

            # box A
            self.canvas.create_rectangle(
                base_x, a_y1, base_x + box_w, a_y1 + box_h_small,
                fill=BOX_FILL, outline=BOX_OUTLINE, width=self.line_width
            )

            self.canvas.create_text(
                base_x + box_w/2,
                a_y1 + box_h_small/2,
                text=self.third_place["a"],
                font=("Arial", cell_font_size)
            )

            # box B
            self.canvas.create_rectangle(
                base_x, b_y1, base_x + box_w, b_y1 + box_h_small,
                fill=BOX_FILL, outline=BOX_OUTLINE, width=self.line_width
            )

            self.canvas.create_text(
                base_x + box_w/2,
                b_y1 + box_h_small/2,
                text=self.third_place["b"],
                font=("Arial", cell_font_size)
            )

            # --- WINNER BOX ---
            win_y1 = a_y1

            self.canvas.create_rectangle(
                win_x, win_y1,
                win_x + winner_w, win_y1 + winner_h,
                fill=BOX_FILL, outline=BOX_OUTLINE, width=self.line_width
            )

            self.canvas.create_text(
                win_x + winner_w/2,
                win_y1 + winner_h/2,
                text=self.third_place["winner"],
                font=("Arial", cell_font_size*2, "bold")
            )

            # highlight clear fields
            if not self.third_place["a"].strip():
                self.canvas.create_rectangle(
                    base_x, a_y1, base_x + box_w, a_y1 + box_h_small,
                    fill=WINNER_FILL, outline="", width=0
                )

            if not self.third_place["b"].strip():
                self.canvas.create_rectangle(
                    base_x, b_y1, base_x + box_w, b_y1 + box_h_small,
                    fill=WINNER_FILL, outline="", width=0
                )

            # --- LINE ---
            self.canvas.create_line(
                base_x + box_w,
                a_y1 + box_h_small,
                win_x,
                win_y1 + winner_h/2,
                fill=THIRD_PLACE_LINE_COLOR,
                width=self.line_width
            )

            # --- LINES from semifinal to 3. place ---
            if len(semi_losers_centers) >= 2:

                p1 = semi_losers_centers[0]
                p2 = semi_losers_centers[1]

                target_x = base_x

                self.canvas.create_line(
                    p1[0], p1[1],
                    target_x,
                    a_y1 + box_h_small / 2,
                    fill=THIRD_PLACE_LINE_COLOR,
                    width=self.line_width,
                    smooth=True
                )

                self.canvas.create_line(
                    p2[0], p2[1],
                    target_x,
                    b_y1 + box_h_small / 2,
                    fill=THIRD_PLACE_LINE_COLOR,
                    width=self.line_width,
                    smooth=True
                )

            # --- HITBOXES ---
            if not self.lock_edit:

                def edit_tp(field):
                    dlg = tk.Toplevel(self.root)
                    dlg.title("3. místo")

                    ent = tk.Entry(dlg, width=30)
                    ent.pack(padx=10, pady=10)
                    ent.insert(0, self.third_place[field])
                    ent.focus()

                    def ok():
                        self.third_place[field] = ent.get()
                        dlg.destroy()
                        self.redraw()
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
